allanglen/c172-flight-sim-panel/docs/assets/images/bendix-king-kt76c/bendix_king_kt76c_faceplate.jpg

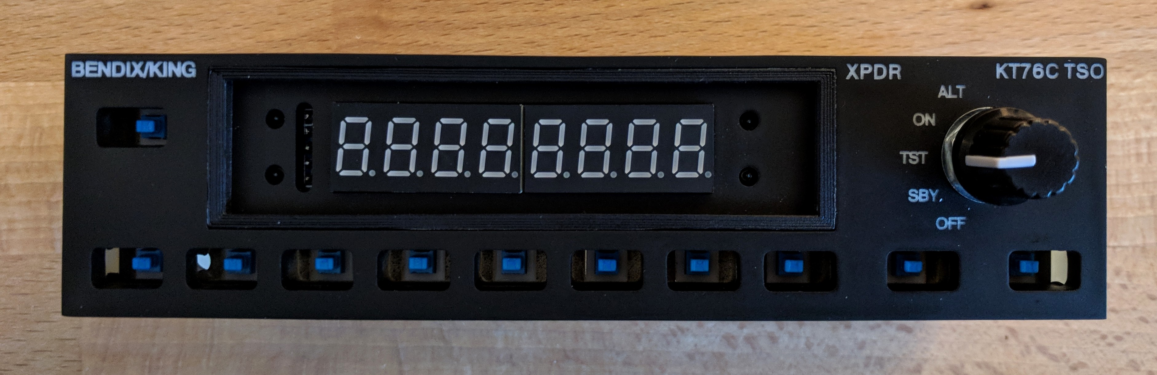
docs/assets/images/bendix-king-kt76c/bendix_king_kt76c_faceplate.jpg
