allanglen/c172-flight-sim-panel/docs/assets/images/docs/dusk.jpg

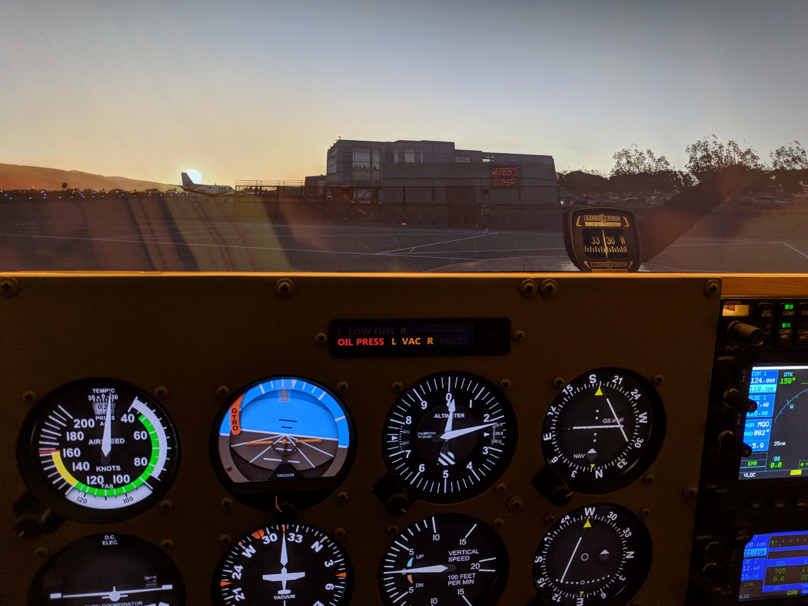
docs/assets/images/docs/dusk.jpg
