allanglen/c172-flight-sim-panel/docs/assets/images/docs/panel_close.jpg

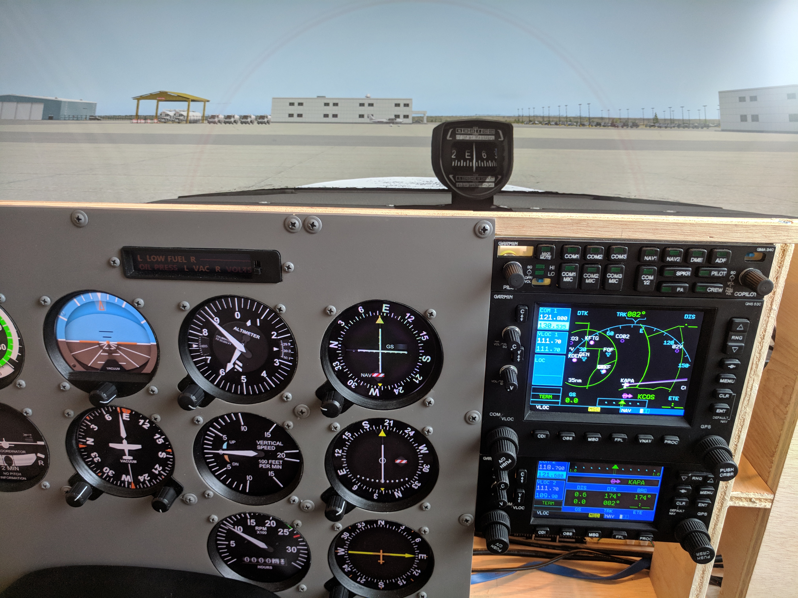
docs/assets/images/docs/panel_close.jpg
