allanglen/c172-flight-sim-panel/docs/assets/images/flap-control-panel/flap_faceplate.jpg

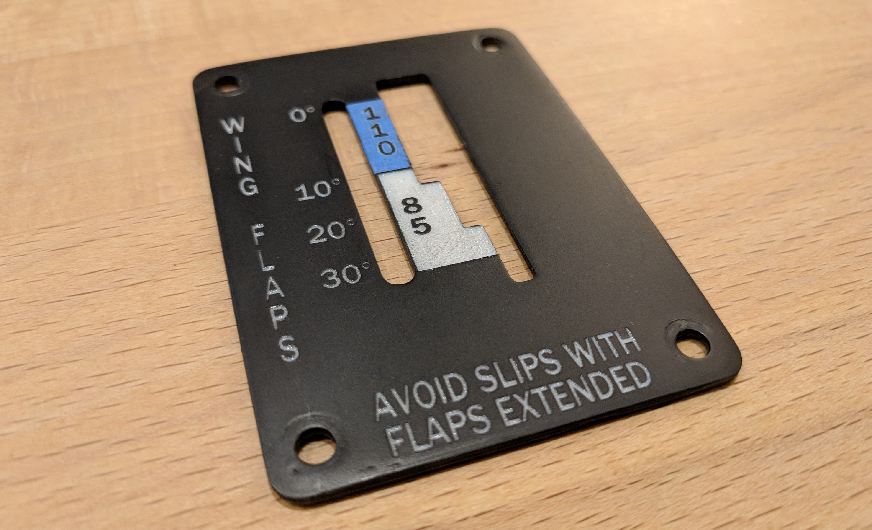
docs/assets/images/flap-control-panel/flap_faceplate.jpg
