allanglen/c172-flight-sim-panel/docs/assets/images/flap-control-panel/flap_lever_mount_rear.jpg

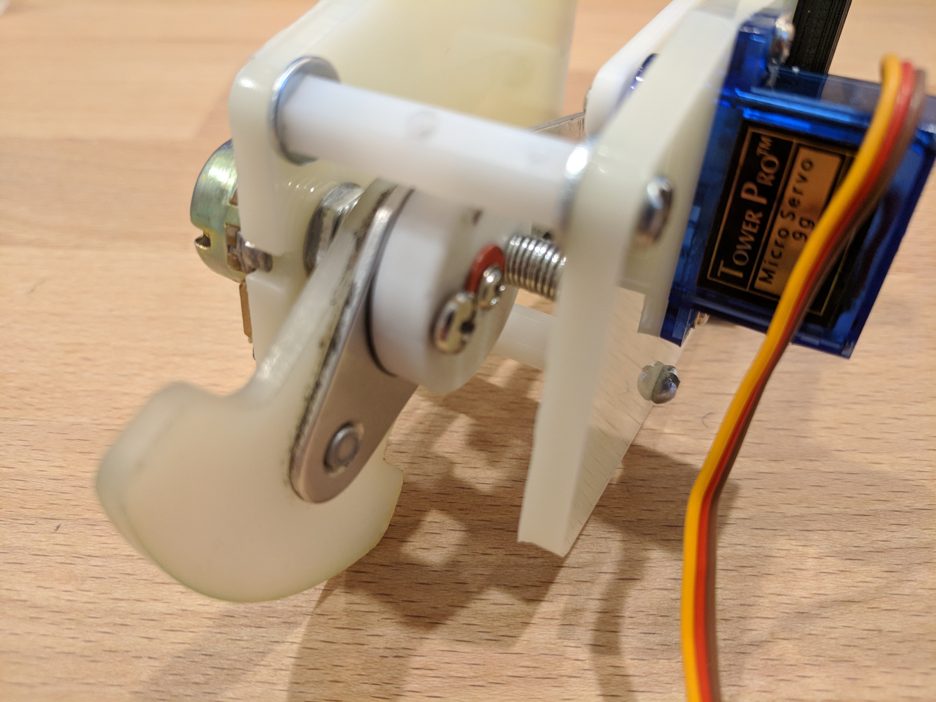
docs/assets/images/flap-control-panel/flap_lever_mount_rear.jpg
