allanglen/c172-flight-sim-panel/docs/assets/images/flap-control-panel/flaps_frame.jpg

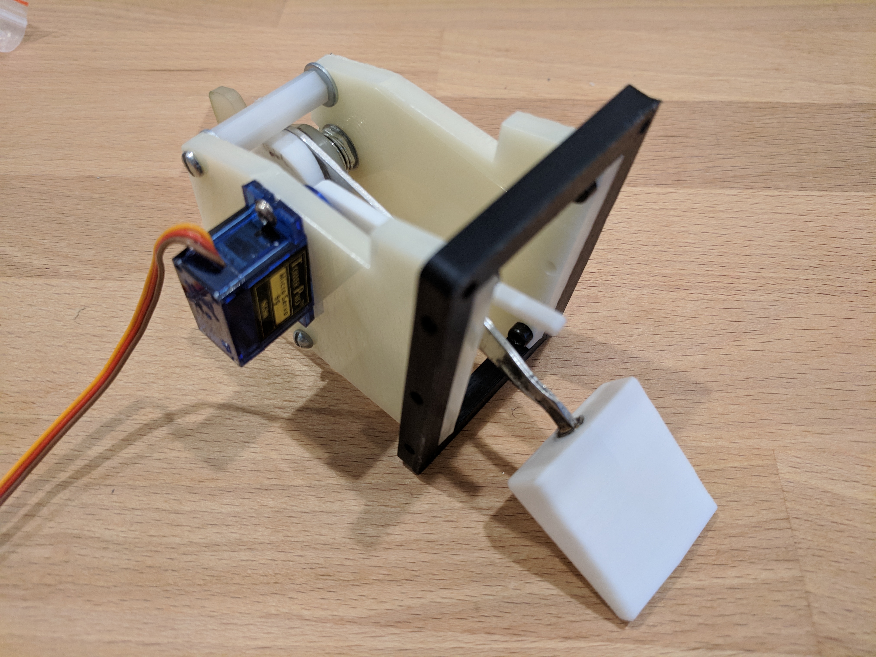
docs/assets/images/flap-control-panel/flaps_frame.jpg
