allanglen/c172-flight-sim-panel/docs/assets/images/flap-control-panel/flaps_panel.jpg

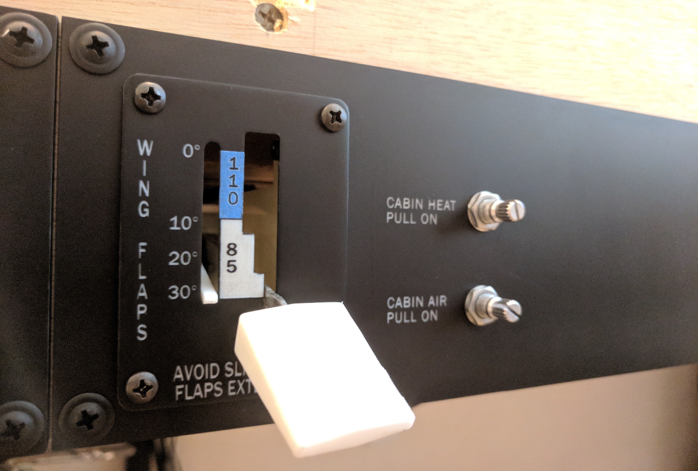
docs/assets/images/flap-control-panel/flaps_panel.jpg
