allanglen/c172-flight-sim-panel/docs/assets/images/flap-control-panel/frame_mounting_bracket.jpg

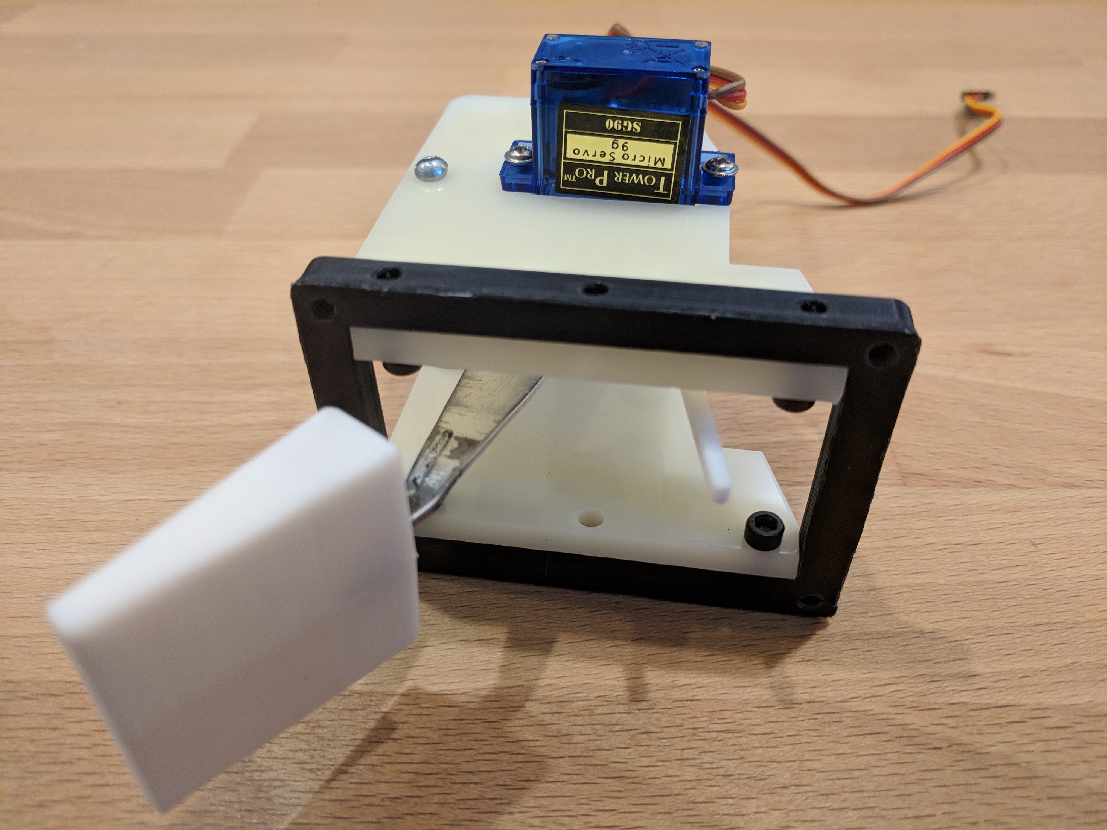
docs/assets/images/flap-control-panel/frame_mounting_bracket.jpg
