allanglen/c172-flight-sim-panel/docs/assets/images/frame/frame.jpg

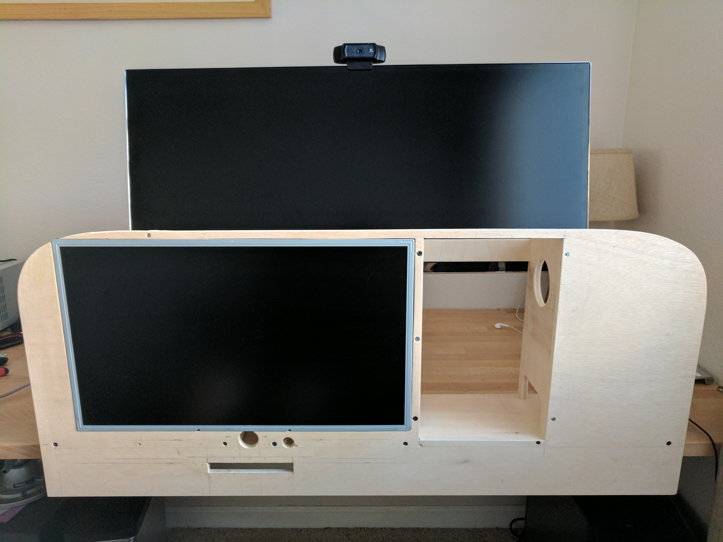
docs/assets/images/frame/frame.jpg
