allanglen/c172-flight-sim-panel/docs/assets/images/garmin-gns-430/display_rear.jpg

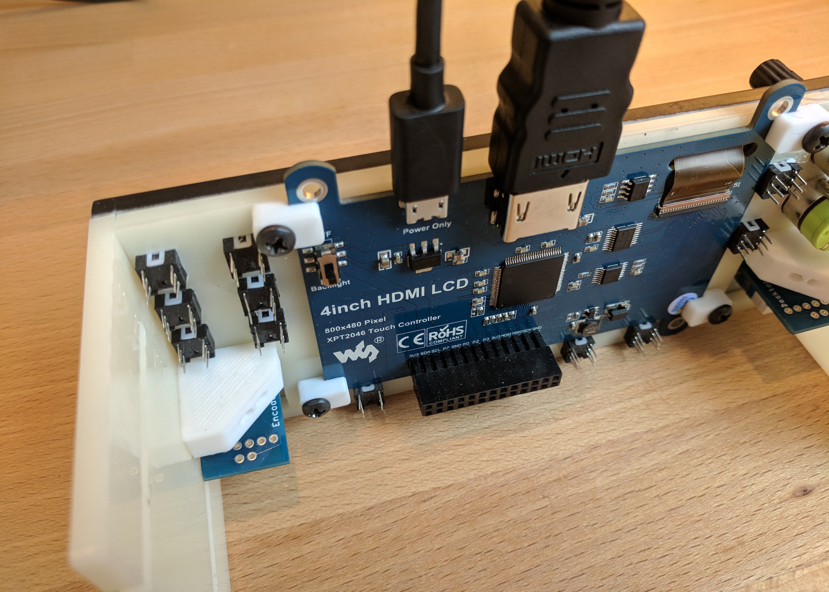
docs/assets/images/garmin-gns-430/display_rear.jpg
