allanglen/c172-flight-sim-panel/docs/assets/images/garmin-gns-430/frame_mount.jpg

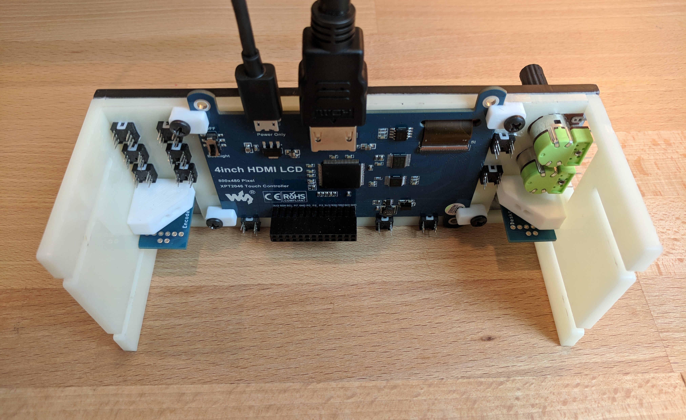
docs/assets/images/garmin-gns-430/frame_mount.jpg
