allanglen/c172-flight-sim-panel/docs/assets/images/garmin-gns-430/garmin_gns_430_map.jpg

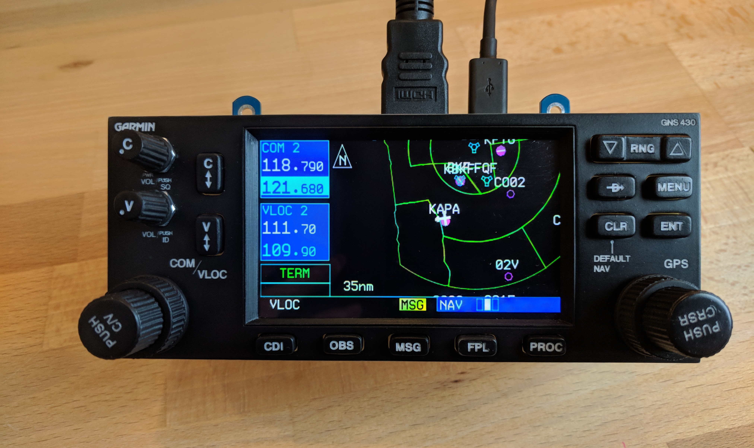
docs/assets/images/garmin-gns-430/garmin_gns_430_map.jpg
