allanglen/c172-flight-sim-panel/docs/assets/images/garmin-gns-430/garmin_gns_430_mounted_stack.jpg

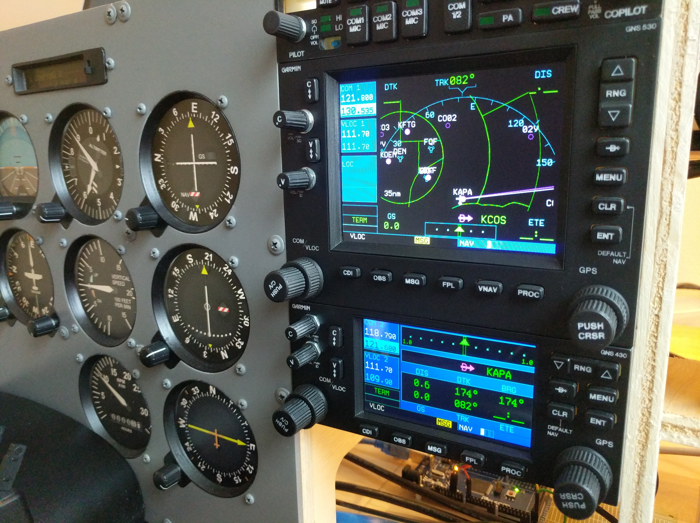
docs/assets/images/garmin-gns-430/garmin_gns_430_mounted_stack.jpg
