allanglen/c172-flight-sim-panel/docs/assets/images/garmin-gns-430/knob.jpg

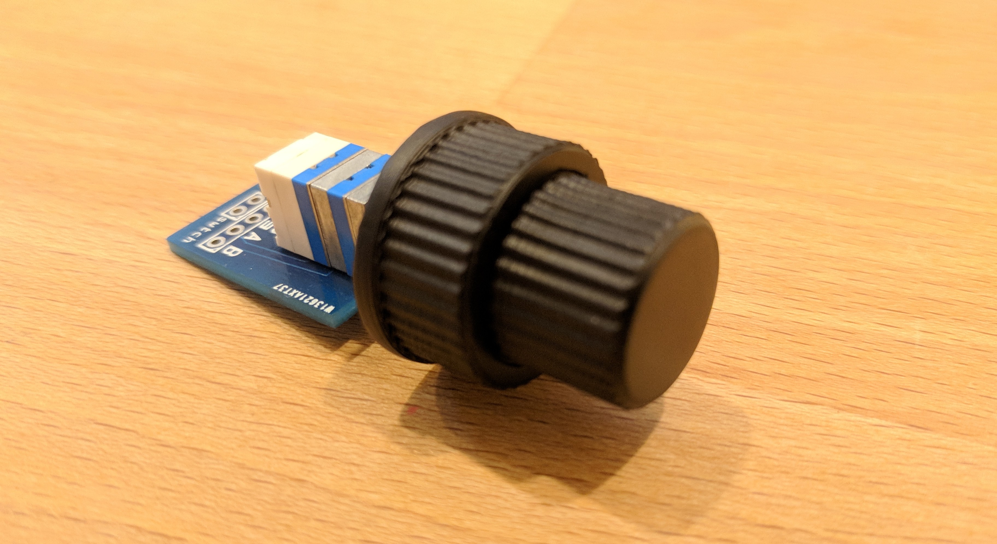
docs/assets/images/garmin-gns-430/knob.jpg
