allanglen/c172-flight-sim-panel/docs/assets/images/garmin-gns-530/frame_mount_left.jpg

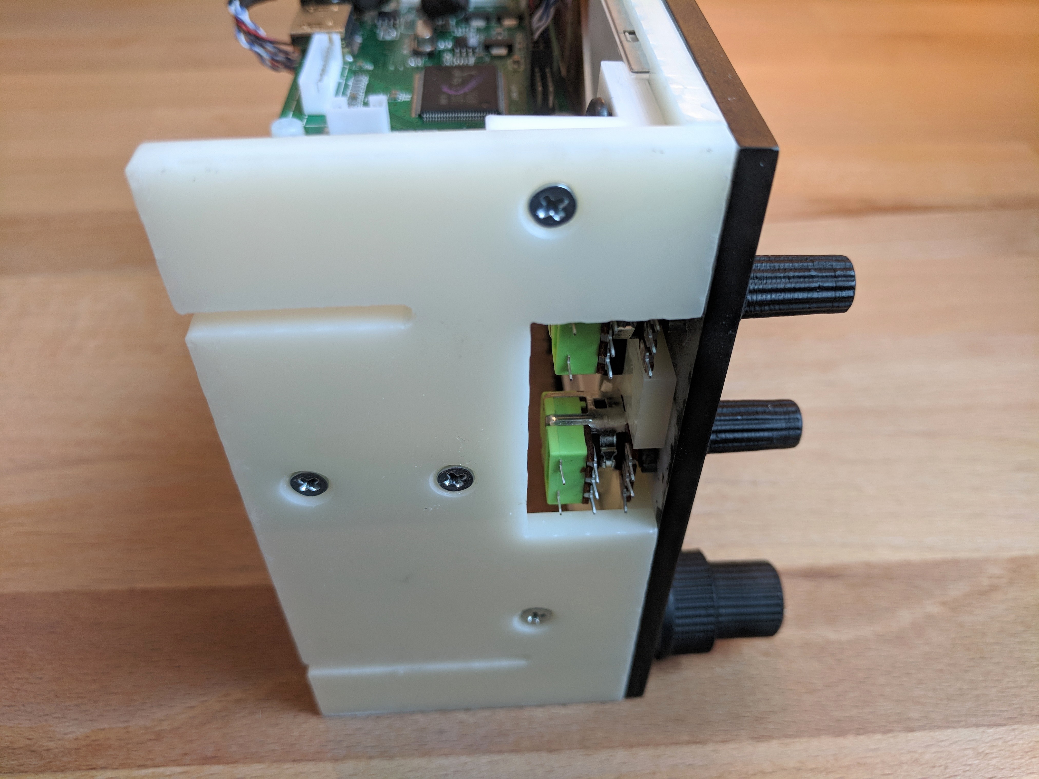
docs/assets/images/garmin-gns-530/frame_mount_left.jpg
