allanglen/c172-flight-sim-panel/docs/assets/images/garmin-gns-530/garmin_gns_530_mounted.jpg

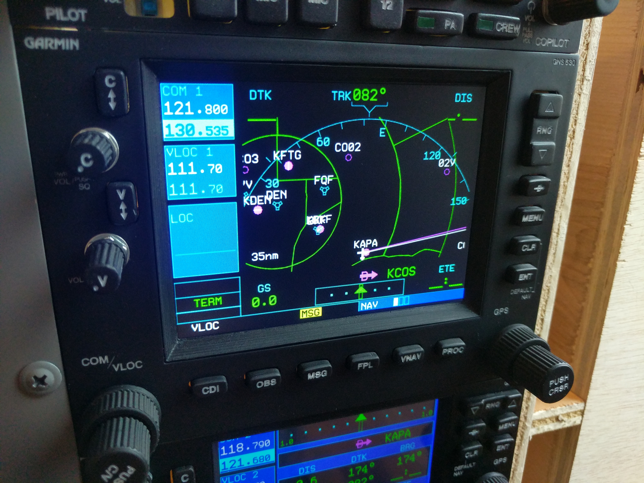
docs/assets/images/garmin-gns-530/garmin_gns_530_mounted.jpg
