allanglen/c172-flight-sim-panel/docs/assets/images/garmin-gns-530/garmin_gns_530_multiplexer.jpg

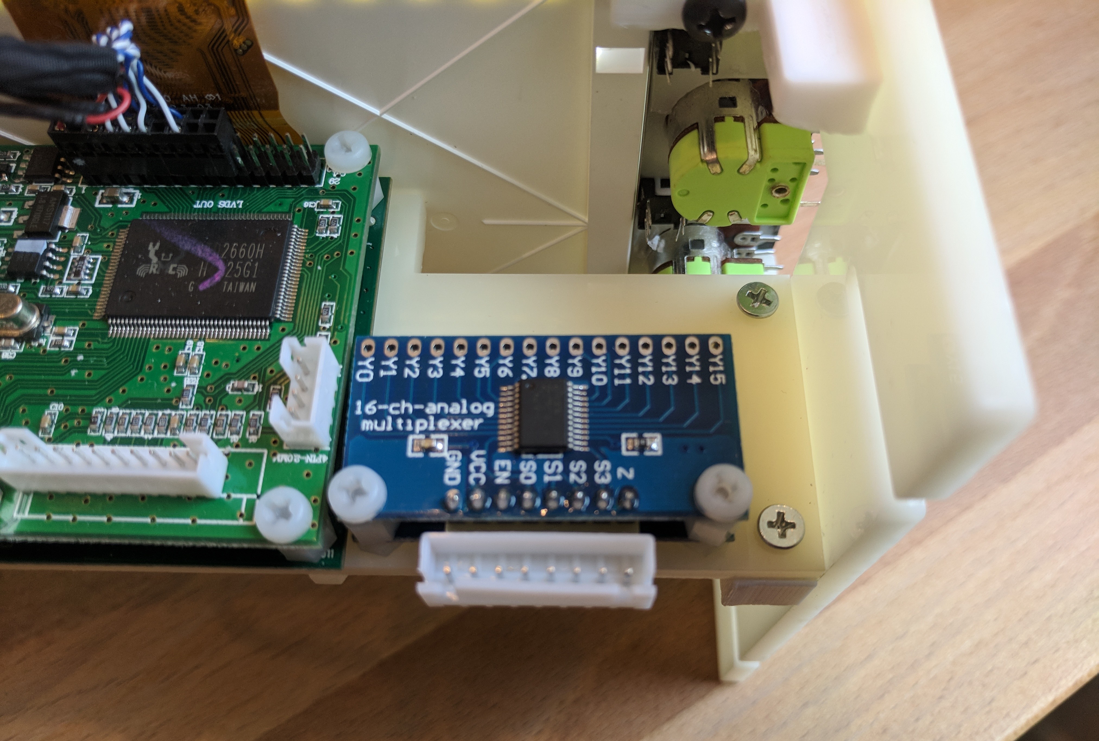
docs/assets/images/garmin-gns-530/garmin_gns_530_multiplexer.jpg
