allanglen/c172-flight-sim-panel/docs/assets/images/hero.jpg

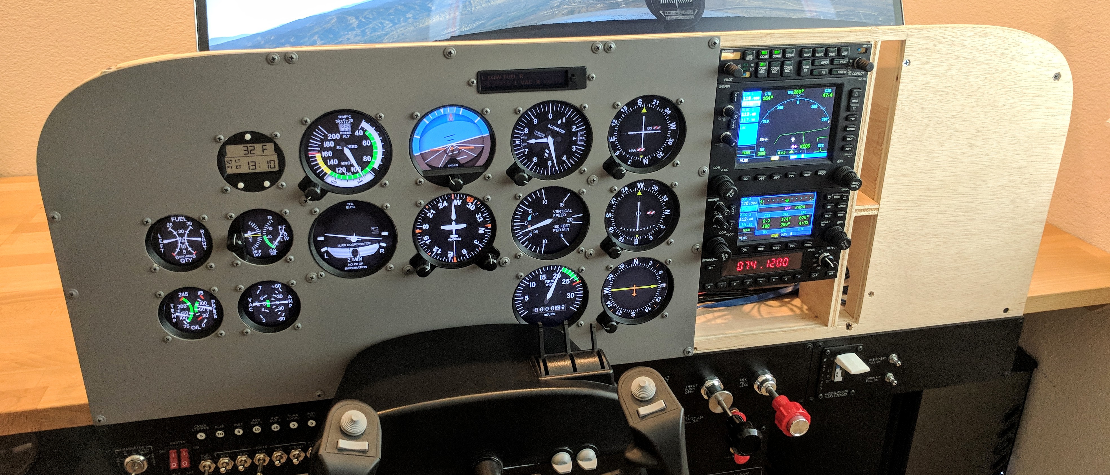
docs/assets/images/hero.jpg
