allanglen/c172-flight-sim-panel/docs/assets/images/highlight-avionics.jpg

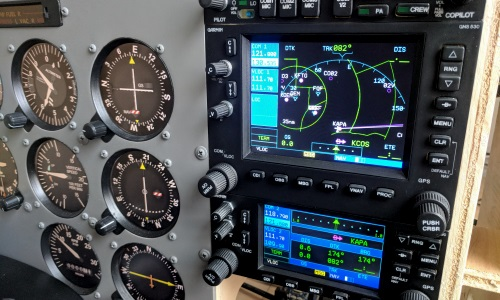
docs/assets/images/highlight-avionics.jpg
