allanglen/c172-flight-sim-panel/docs/assets/images/highlight-instrument-panel.jpg

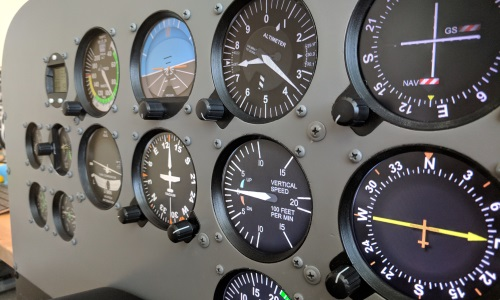
docs/assets/images/highlight-instrument-panel.jpg
