allanglen/c172-flight-sim-panel/docs/assets/images/highlight-switch-panel.jpg

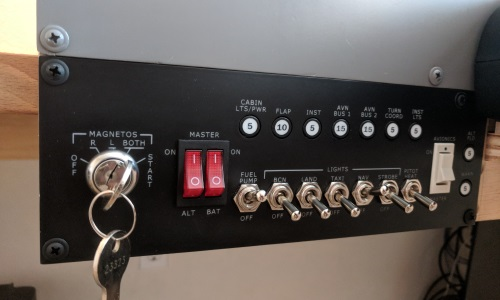
docs/assets/images/highlight-switch-panel.jpg
