allanglen/c172-flight-sim-panel/docs/assets/images/instrument-panel/air_manager.jpg

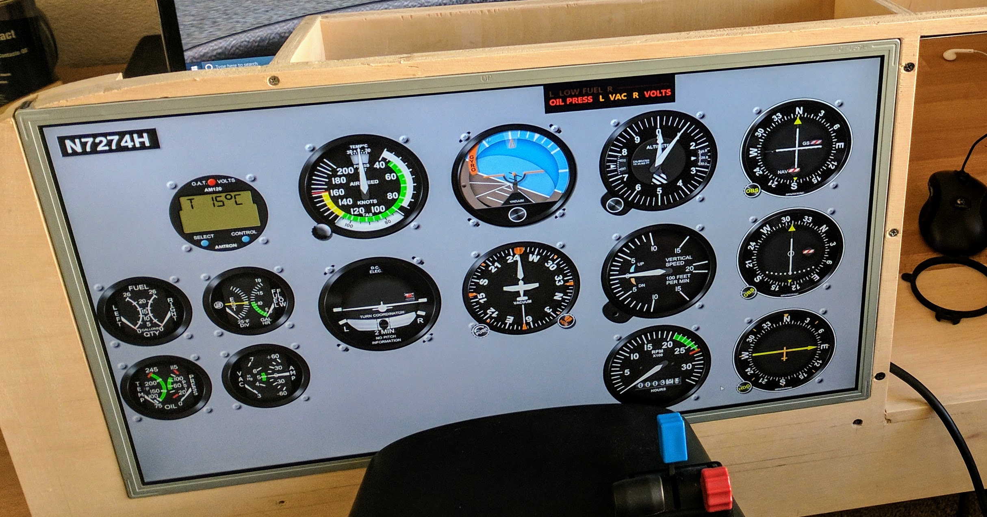
docs/assets/images/instrument-panel/air_manager.jpg
