allanglen/c172-flight-sim-panel/docs/assets/images/instrument-panel/bezel_encoder.jpg

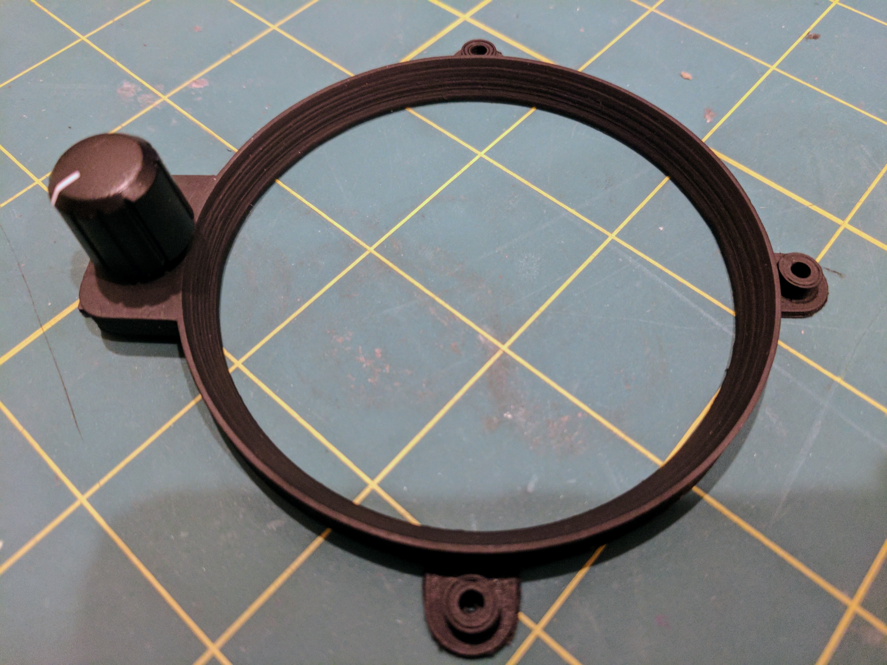
docs/assets/images/instrument-panel/bezel_encoder.jpg
