allanglen/c172-flight-sim-panel/docs/assets/images/instrument-panel/bezel_lcd.jpg

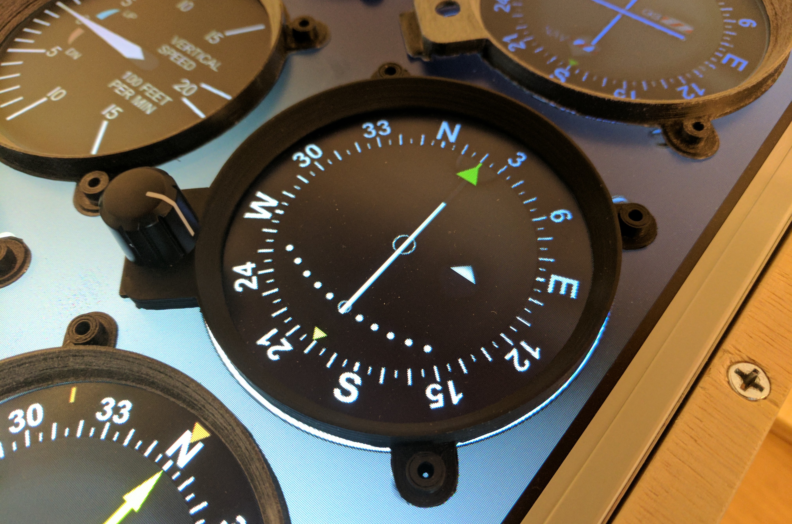
docs/assets/images/instrument-panel/bezel_lcd.jpg
