allanglen/c172-flight-sim-panel/docs/assets/images/instrument-panel/display_03.jpg

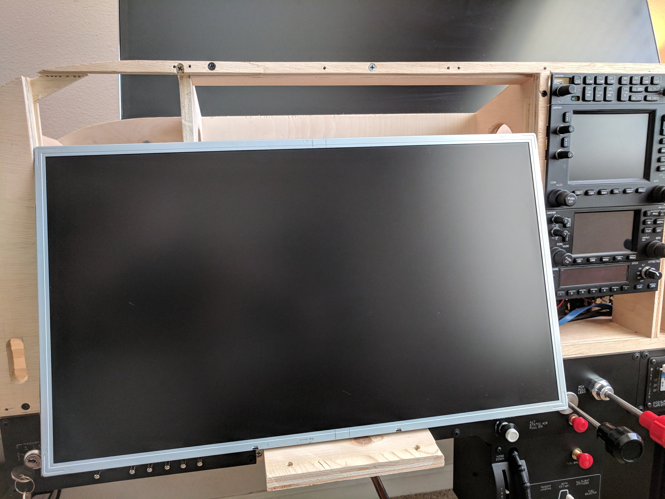
docs/assets/images/instrument-panel/display_03.jpg
