allanglen/c172-flight-sim-panel/docs/assets/images/instrument-panel/display_04.jpg

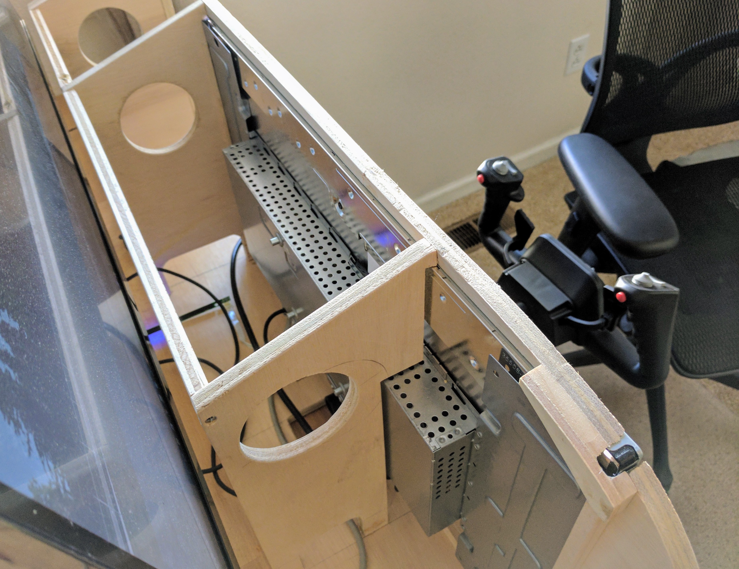
docs/assets/images/instrument-panel/display_04.jpg
