allanglen/c172-flight-sim-panel/docs/assets/images/instrument-panel/instrument_display.jpg

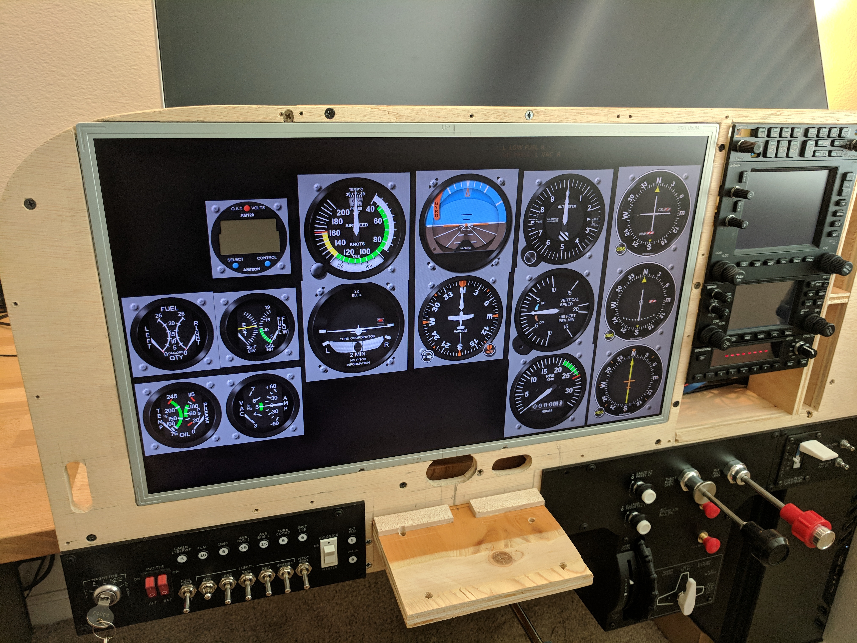
docs/assets/images/instrument-panel/instrument_display.jpg
