allanglen/c172-flight-sim-panel/docs/assets/images/instrument-panel/instrument_panel.jpg

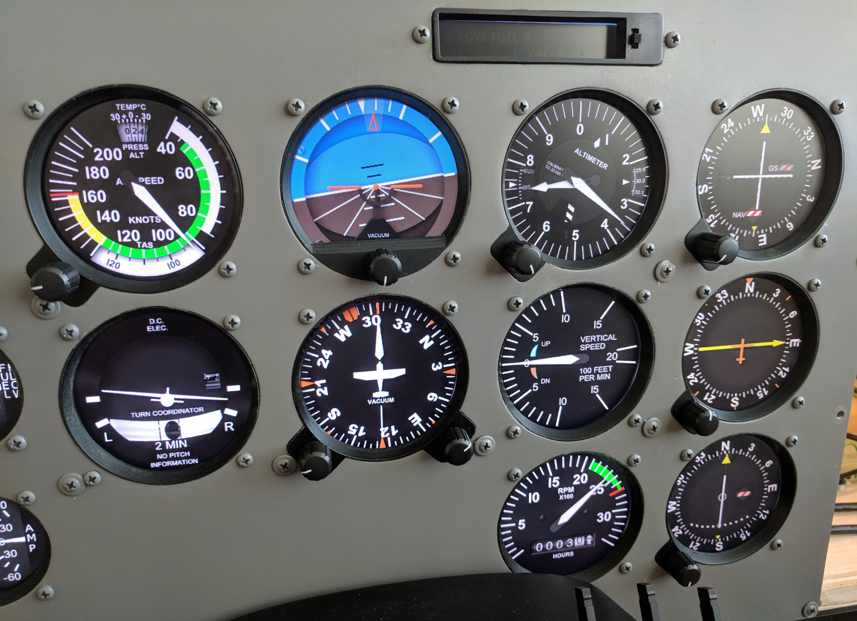
docs/assets/images/instrument-panel/instrument_panel.jpg
