allanglen/c172-flight-sim-panel/docs/assets/images/instrument-panel/instrument_panel_03.jpg

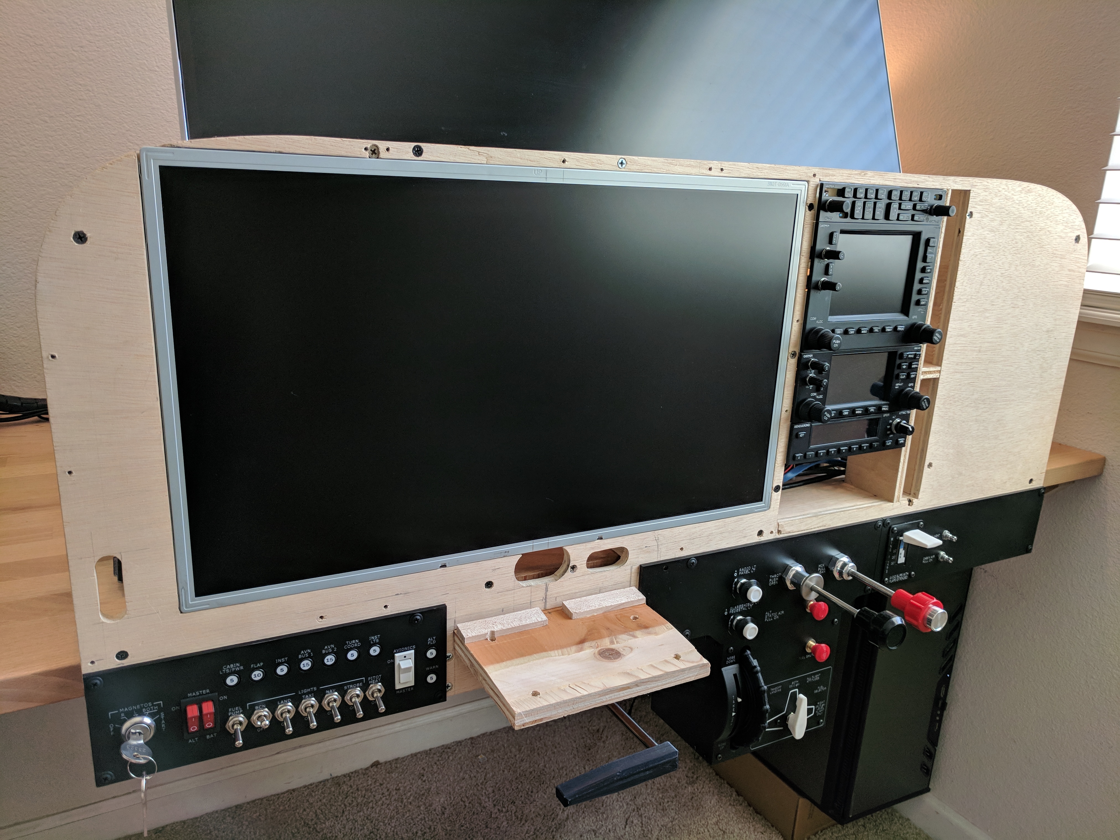
docs/assets/images/instrument-panel/instrument_panel_03.jpg
