allanglen/c172-flight-sim-panel/docs/assets/images/instrument-panel/panel_02.jpg

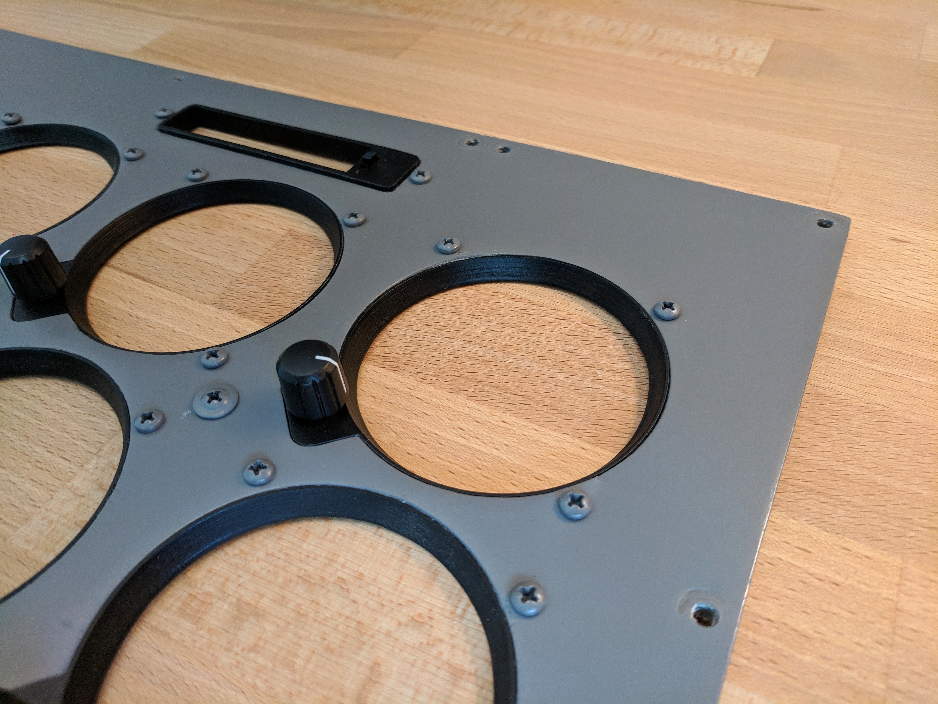
docs/assets/images/instrument-panel/panel_02.jpg
