allanglen/c172-flight-sim-panel/docs/assets/images/instrument-panel/panel_attached_02.jpg

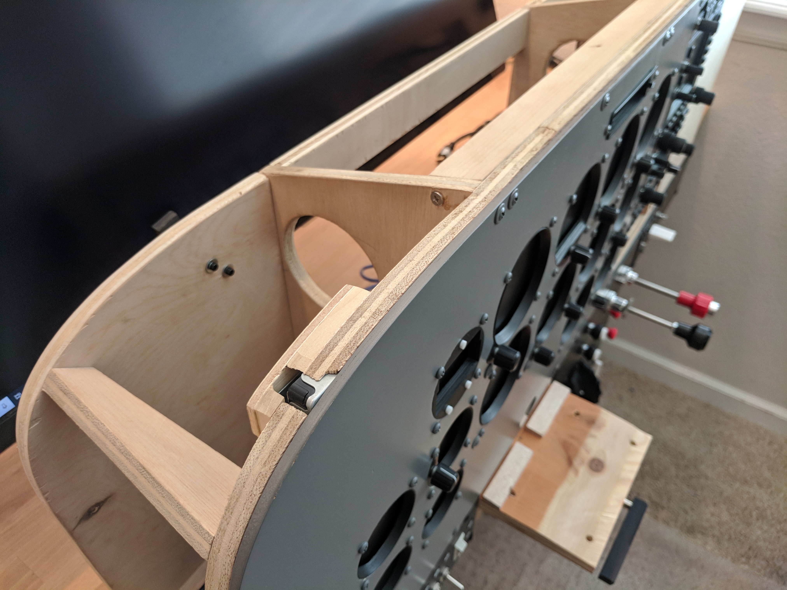
docs/assets/images/instrument-panel/panel_attached_02.jpg
