allanglen/c172-flight-sim-panel/docs/assets/images/instrument-panel/panel_rear_04.jpg

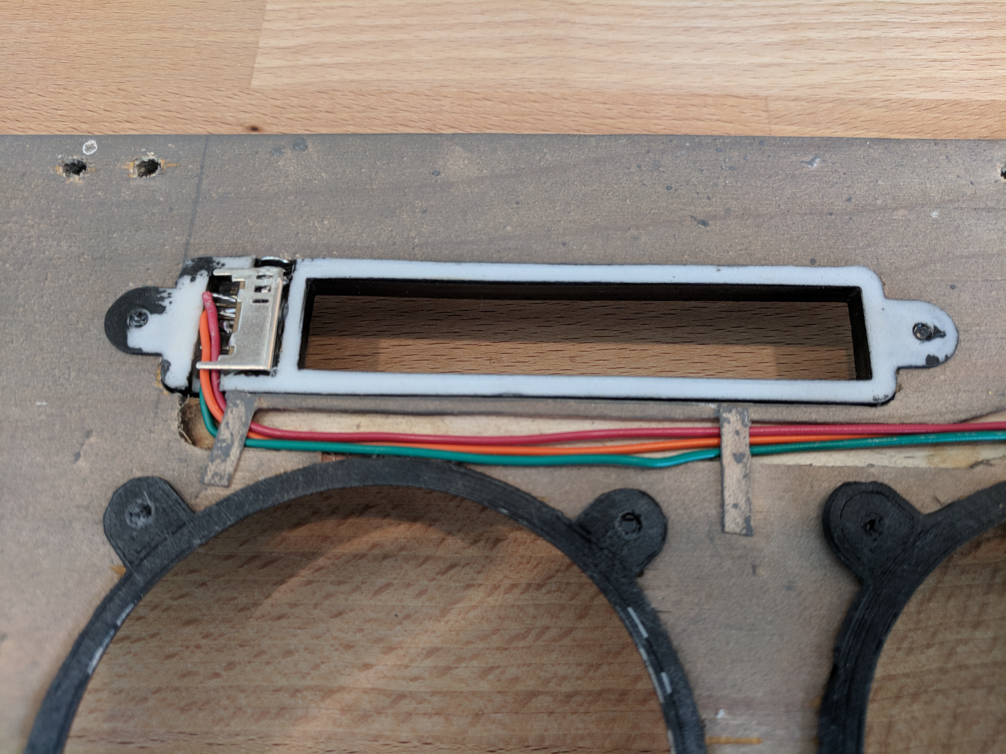
docs/assets/images/instrument-panel/panel_rear_04.jpg
