allanglen/c172-flight-sim-panel/docs/assets/images/instrument-panel/panel_rear_05.jpg

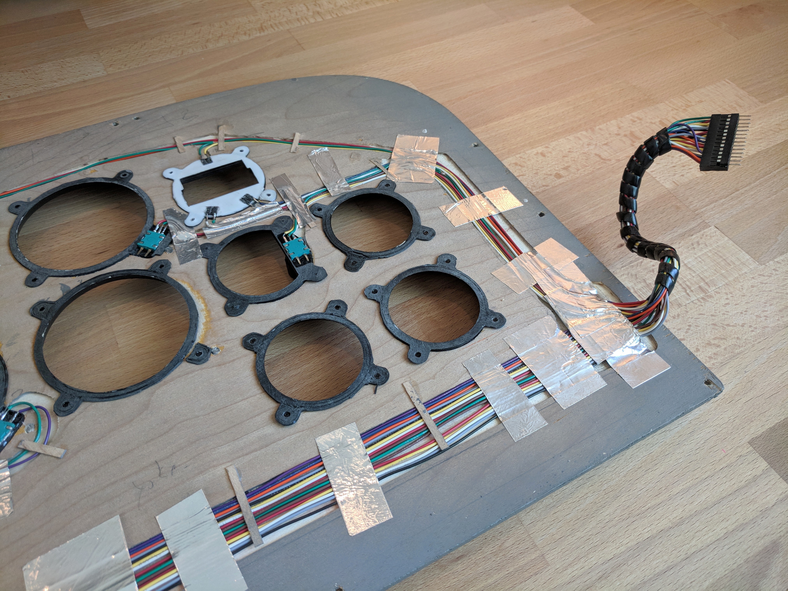
docs/assets/images/instrument-panel/panel_rear_05.jpg
