allanglen/c172-flight-sim-panel/docs/assets/images/key-switch/key_switch_animation.gif

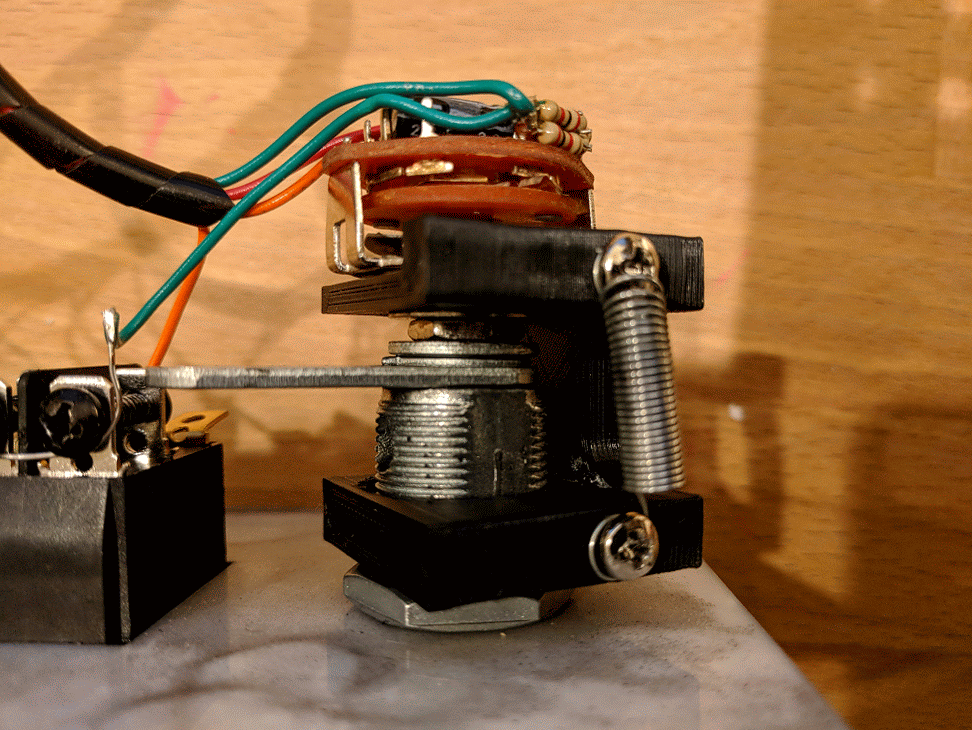
docs/assets/images/key-switch/key_switch_animation.gif
