allanglen/c172-flight-sim-panel/docs/assets/images/key-switch/key_switch_mounted.jpg

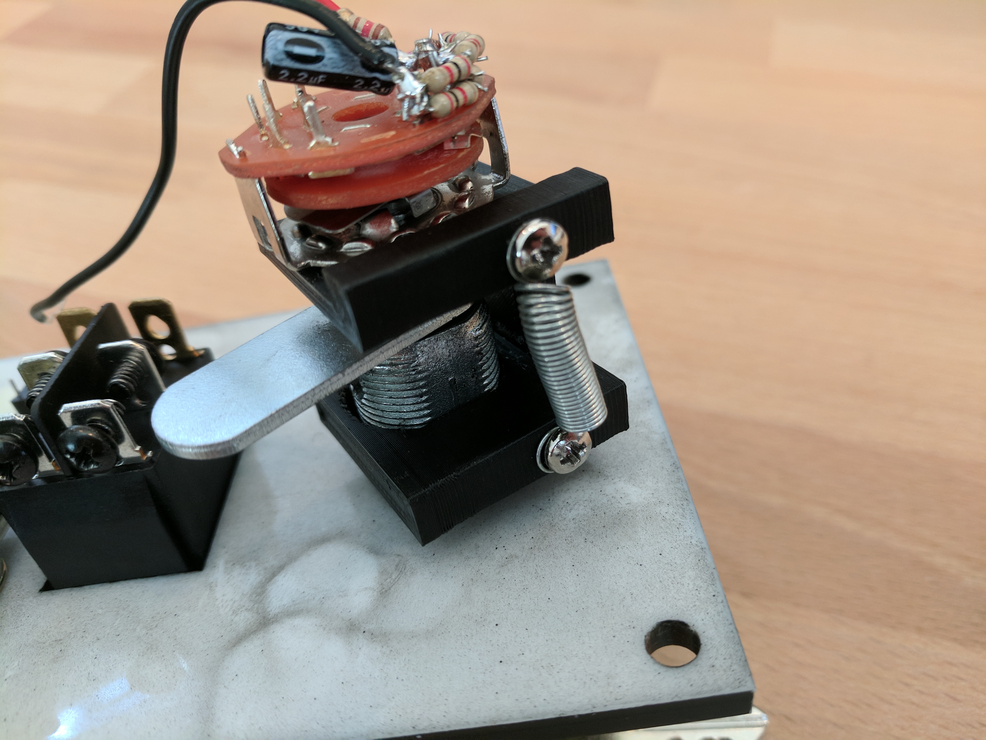
docs/assets/images/key-switch/key_switch_mounted.jpg
