allanglen/c172-flight-sim-panel/docs/assets/images/rudder-pedals/rudder_pedal_left.jpg

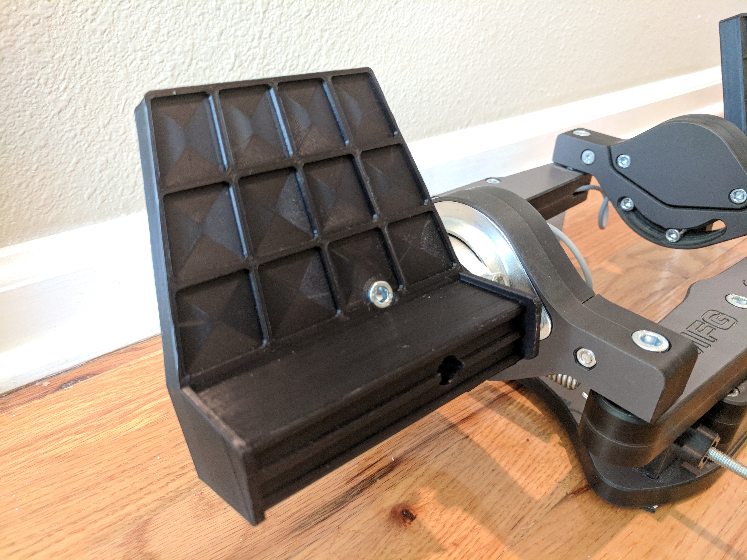
docs/assets/images/rudder-pedals/rudder_pedal_left.jpg
