allanglen/c172-flight-sim-panel/docs/assets/images/rudder-pedals/rudder_pedal_rear.jpg

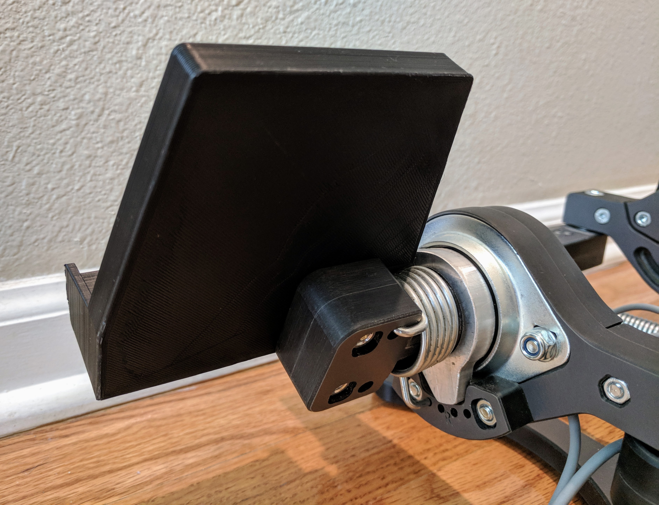
docs/assets/images/rudder-pedals/rudder_pedal_rear.jpg
