allanglen/c172-flight-sim-panel/docs/assets/images/rudder-pedals/rudder_pedal_right.jpg

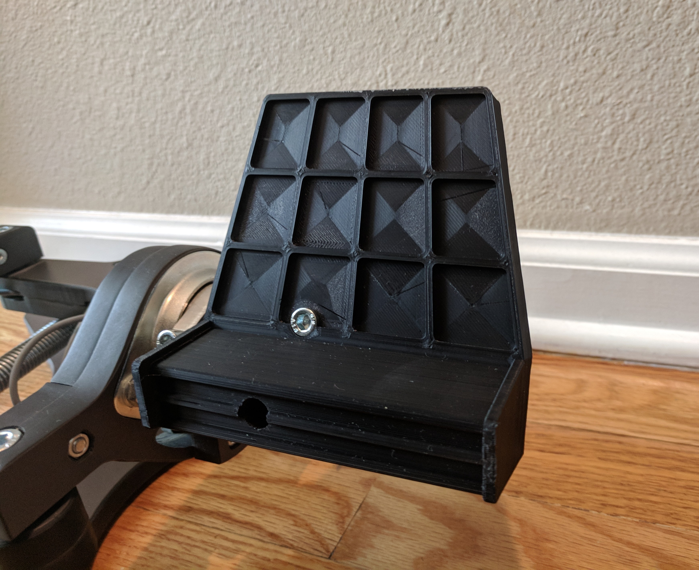
docs/assets/images/rudder-pedals/rudder_pedal_right.jpg
