allanglen/c172-flight-sim-panel/docs/assets/images/rudder-pedals/rudder_pedals.jpg

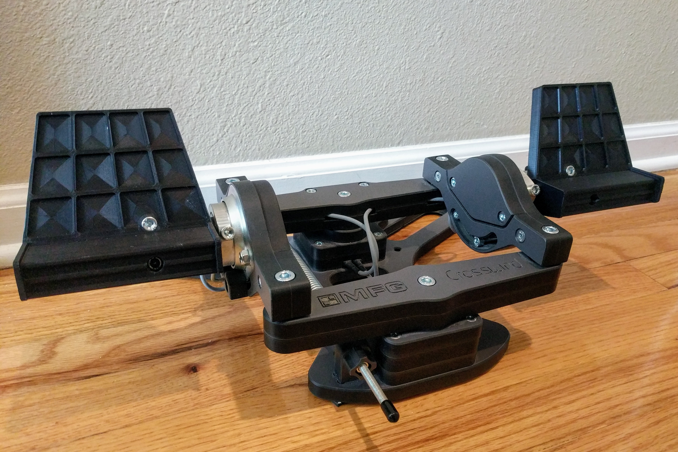
docs/assets/images/rudder-pedals/rudder_pedals.jpg
