allanglen/c172-flight-sim-panel/docs/assets/images/switch-panel/fuse_mount.jpg

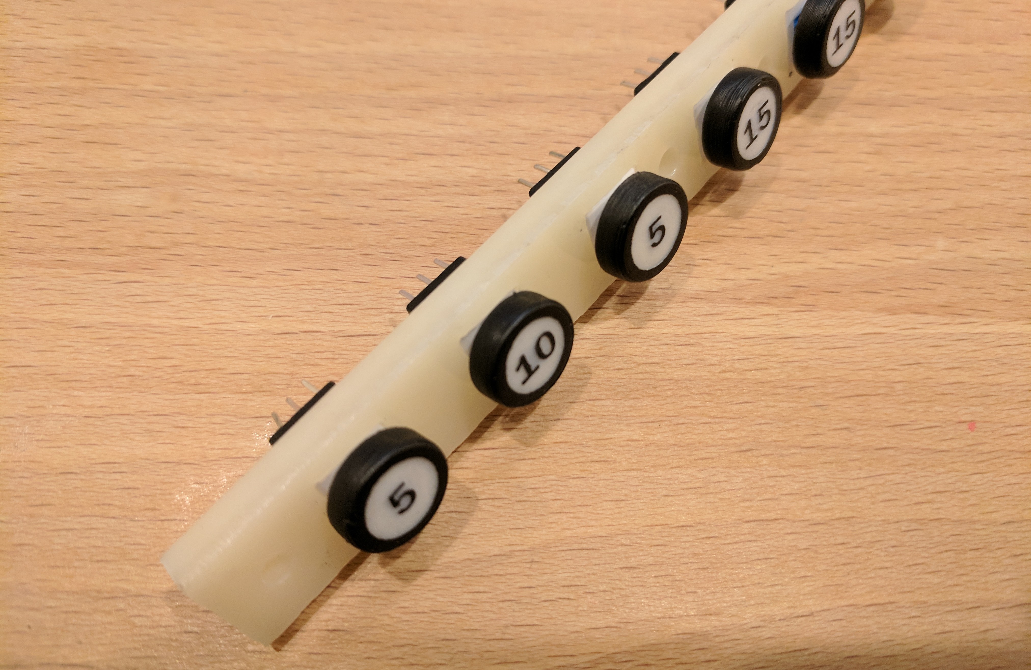
docs/assets/images/switch-panel/fuse_mount.jpg
