allanglen/c172-flight-sim-panel/docs/assets/images/switch-panel/fuses.jpg

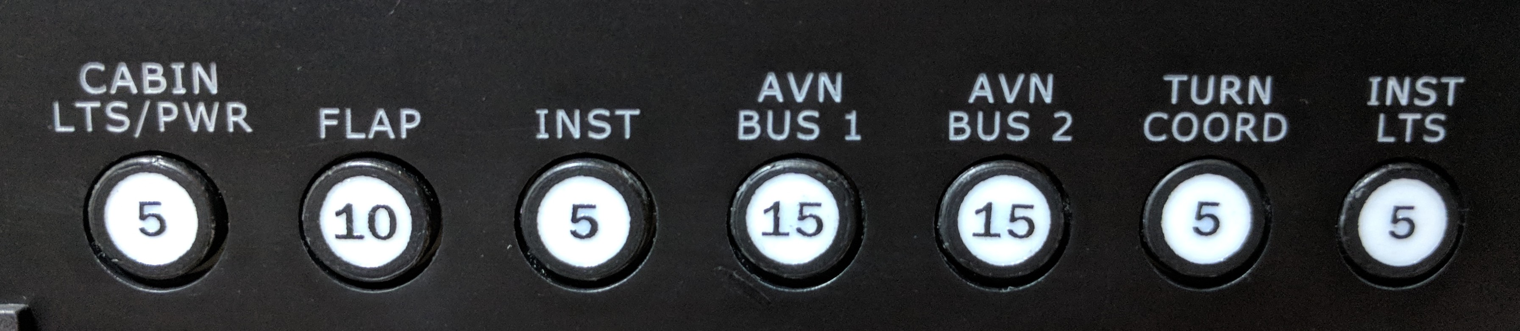
docs/assets/images/switch-panel/fuses.jpg
