allanglen/c172-flight-sim-panel/docs/assets/images/throttle-mixture-panel/rheostat_knobs.jpg

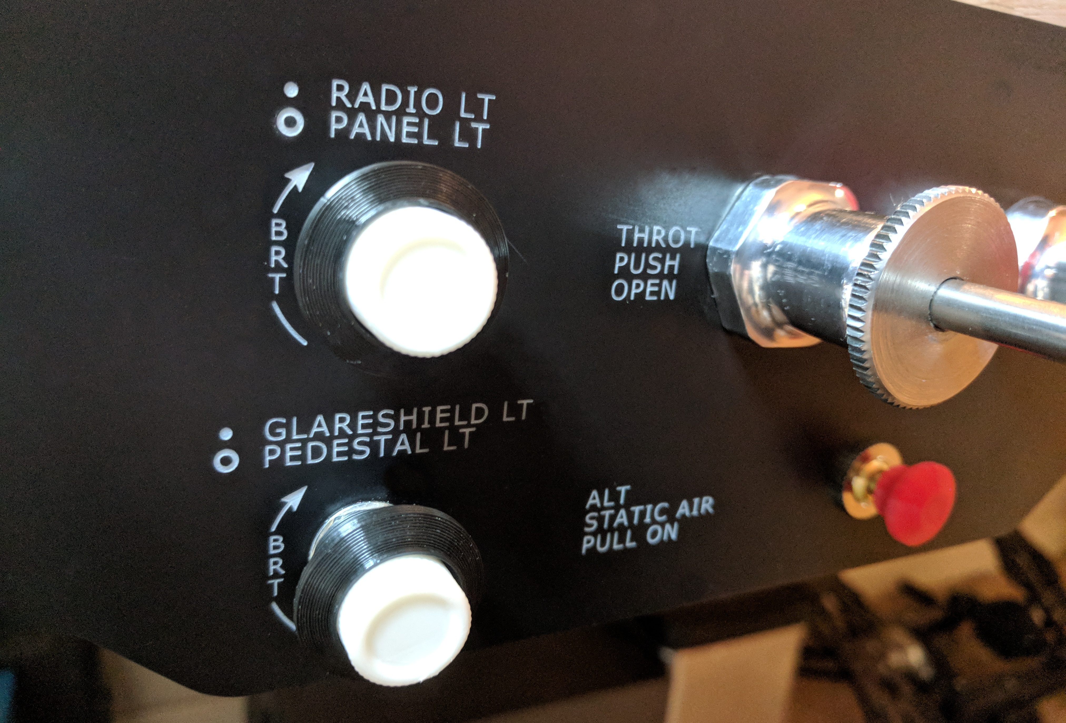
docs/assets/images/throttle-mixture-panel/rheostat_knobs.jpg
