allanglen/c172-flight-sim-panel/docs/assets/images/throttle-mixture-panel/throttle_mixture_panel.jpg

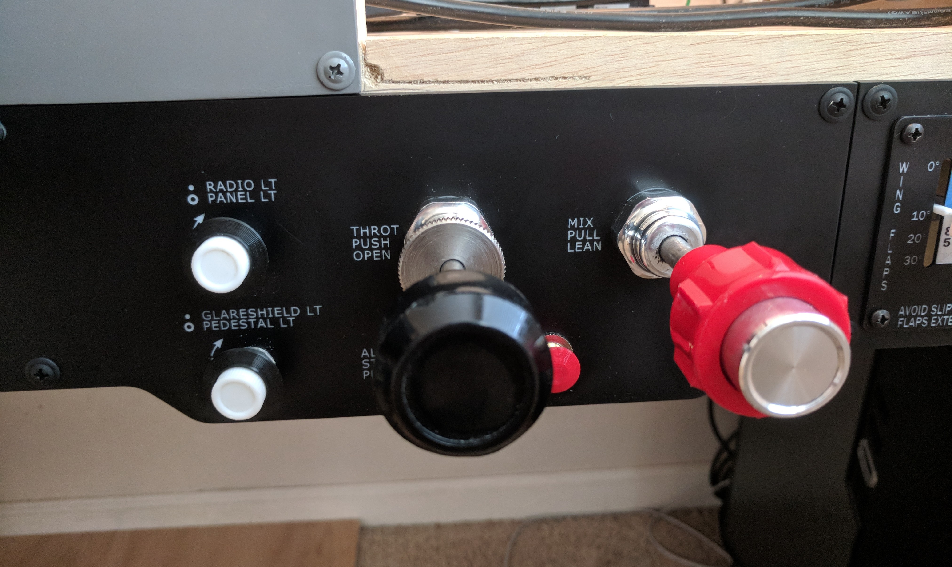
docs/assets/images/throttle-mixture-panel/throttle_mixture_panel.jpg
