allanglen/c172-flight-sim-panel/docs/assets/images/trim-wheel/fuel_selector.jpg

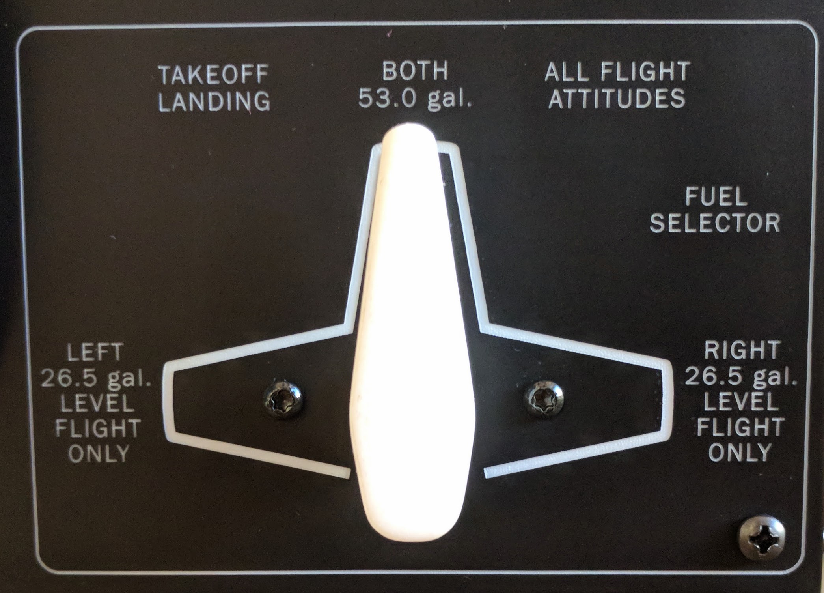
docs/assets/images/trim-wheel/fuel_selector.jpg
