allanglen/c172-flight-sim-panel/docs/assets/images/trim-wheel/trim_wheel_close.jpg

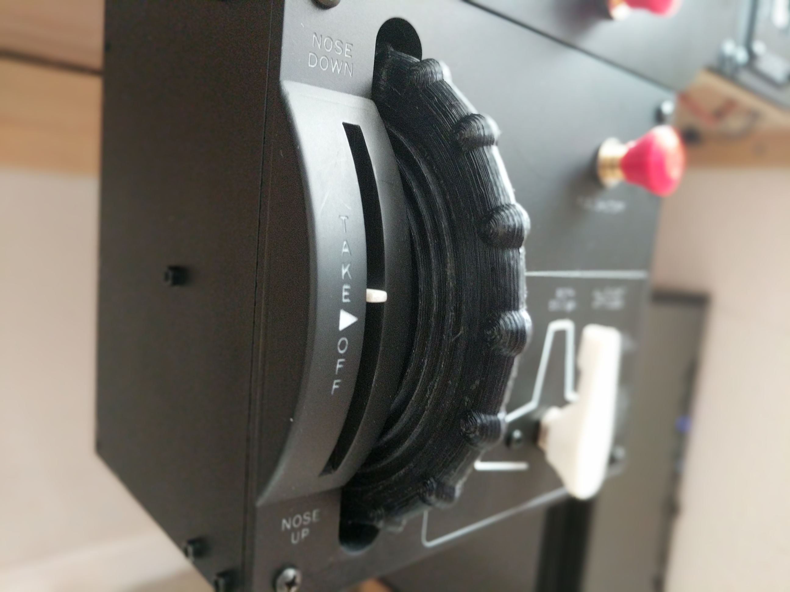
docs/assets/images/trim-wheel/trim_wheel_close.jpg
