allanglen/c172-flight-sim-panel/docs/assets/images/trim-wheel/trim_wheel_faceplate.jpg

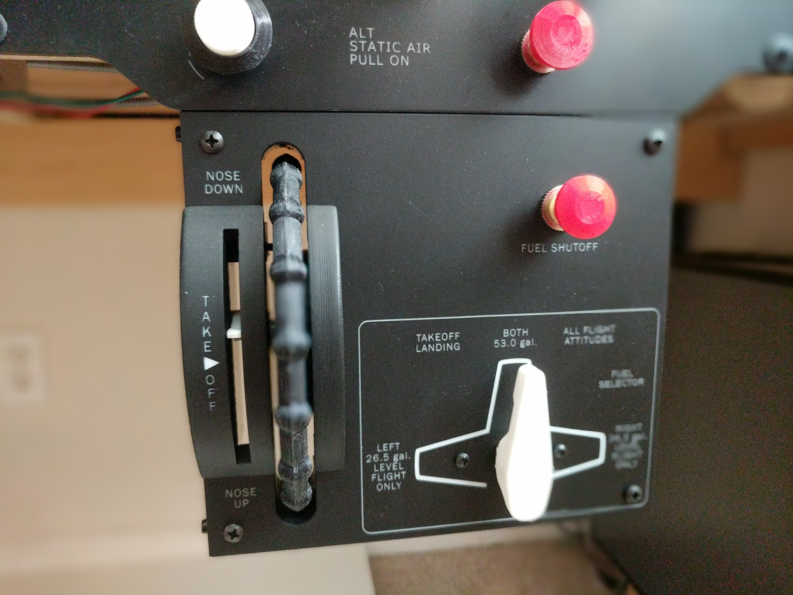
docs/assets/images/trim-wheel/trim_wheel_faceplate.jpg
