allanglen/c172-flight-sim-panel/docs/assets/images/yoke-mount/yoke_mount.jpg

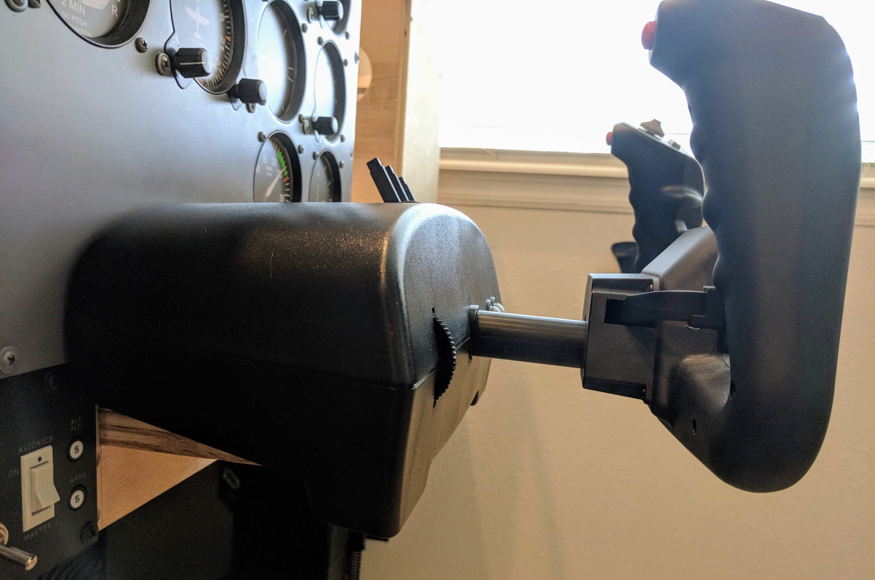
docs/assets/images/yoke-mount/yoke_mount.jpg
