allanglen/c172-flight-sim-panel/instrument_panel/images/instrument_panel_left_view.jpg

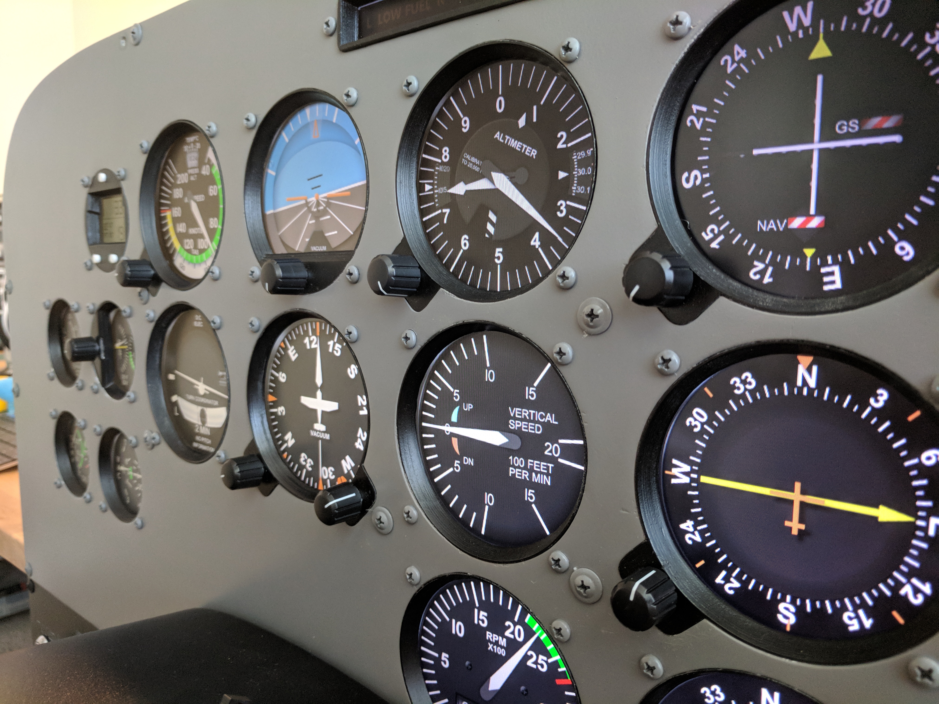
instrument_panel/images/instrument_panel_left_view.jpg
