allanglen/c172-flight-sim-panel/parts/avionics/garmin-gns-430/garmin_430_photo.png

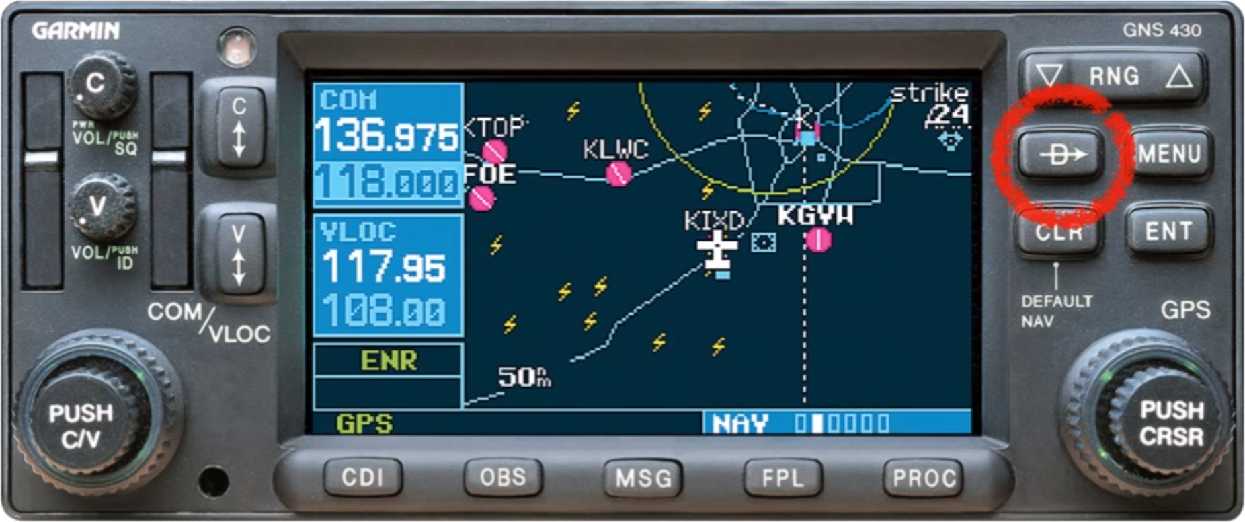
parts/avionics/garmin-gns-430/garmin_430_photo.png
