allanglen/c172-flight-sim-panel/parts/avionics/garmin-gns-530/garmin_gns_530.jpg

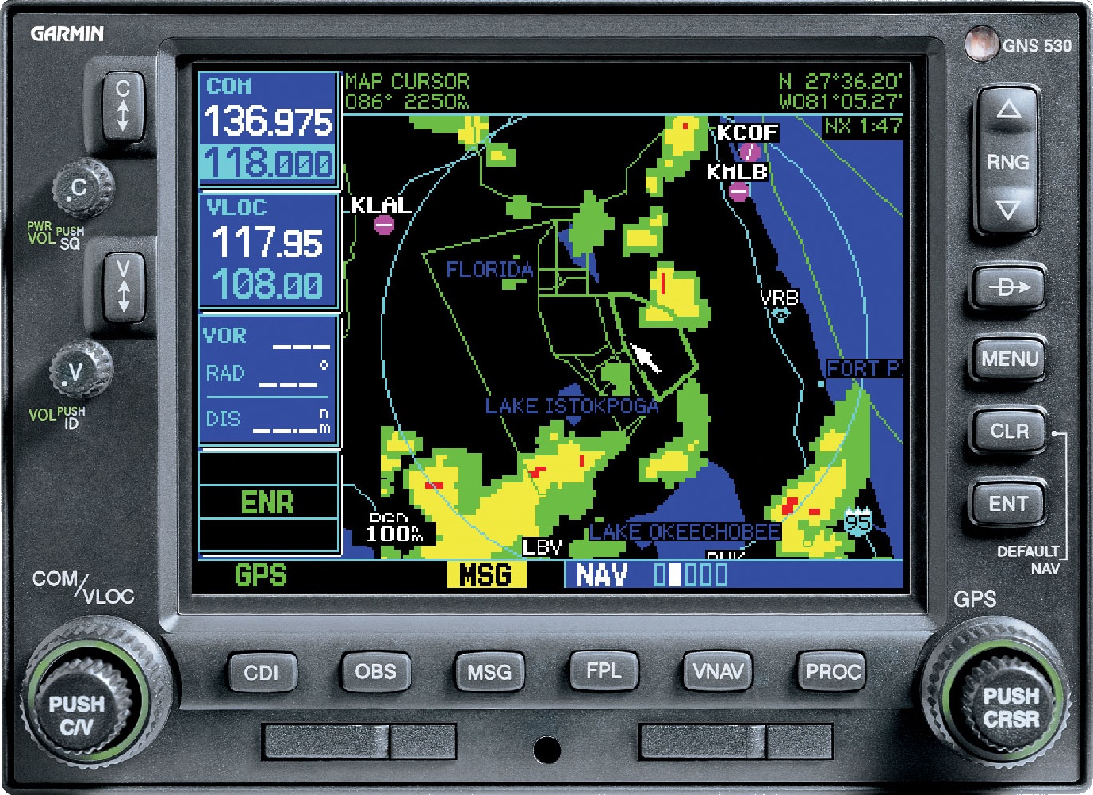
parts/avionics/garmin-gns-530/garmin_gns_530.jpg
