allanglen/c172-flight-sim-panel/parts/throttle-mixture-panel/statis_air_knob.FCStd

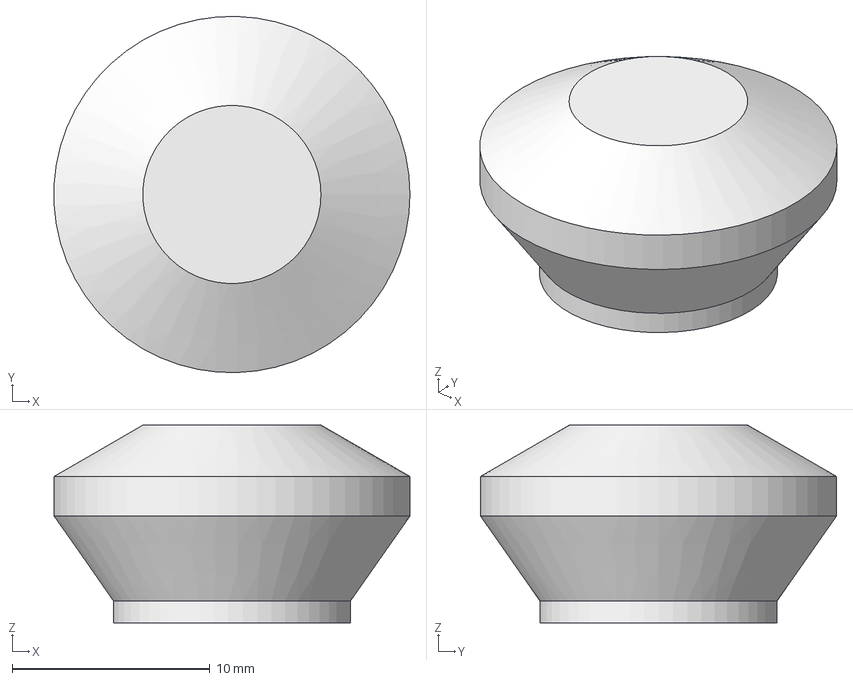
[picture p106: CAD file, 2018-01-21]
parts/throttle-mixture-panel/statis_air_knob.FCStd
18.0 x 18.0 x 10.0 mm
