allanglen/c172-flight-sim-panel/parts/avionics/bendix-king-kt-76c/bendix_king_kt_76c.FCStd

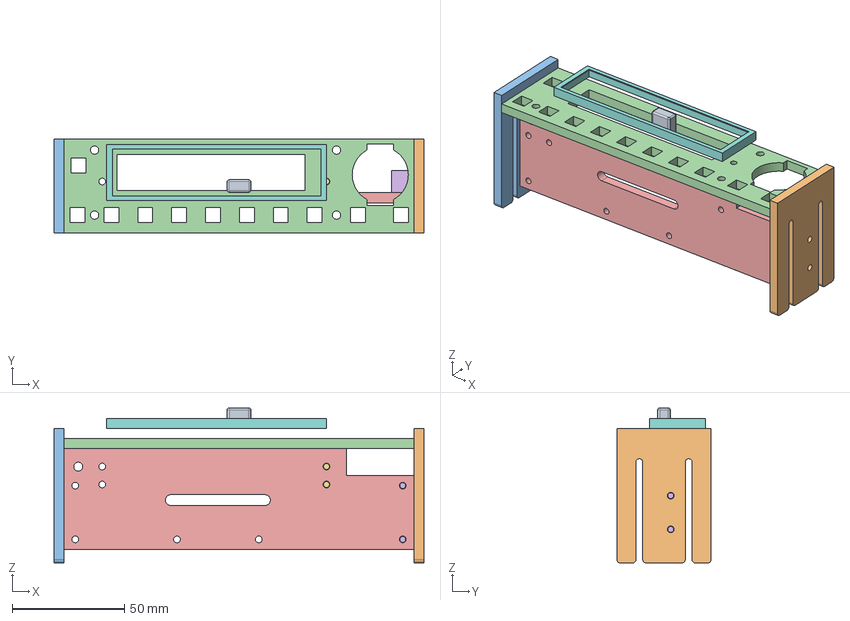
[picture p107: CAD file, 2018-05-28]
parts/avionics/bendix-king-kt-76c/bendix_king_kt_76c.FCStd
165.0 x 42.0 x 69.1 mm
Cut (button)
Pad (right side)
Pad (left side)
Pad (hardware mount)
Pad (electronics mount)
Pocket (side bracket side holes)
Pocket (front bracket front hole)
Cut (bezel)
