allanglen/c172-flight-sim-panel/parts/avionics/garmin-gns-430/preview.stl

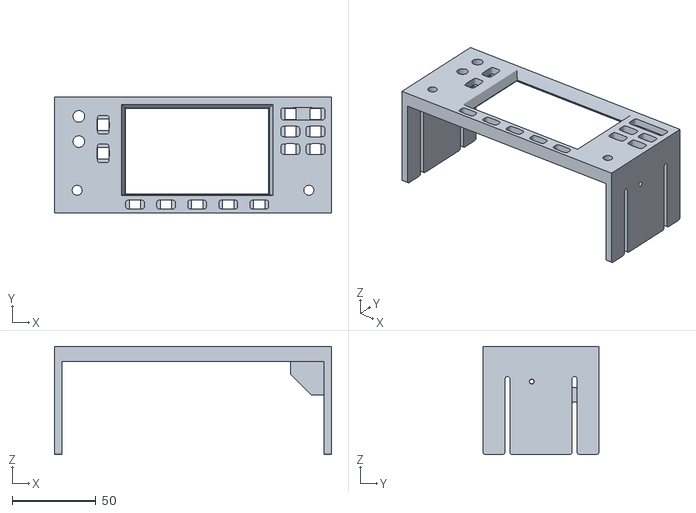
[picture p108: CAD file, 2018-01-07]
parts/avionics/garmin-gns-430/preview.stl
165.0 x 69.0 x 64.5
