allanglen/c172-flight-sim-panel/parts/avionics/garmin-gns-530/preview.stl

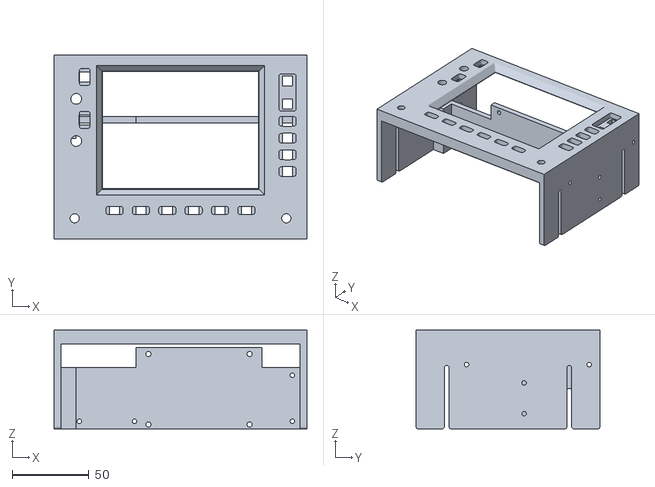
[picture p109: CAD file, 2018-01-21]
parts/avionics/garmin-gns-530/preview.stl
165.0 x 120.0 x 64.5
