allanglen/c172-flight-sim-panel/parts/instrument-panel/bezel_small.FCStd

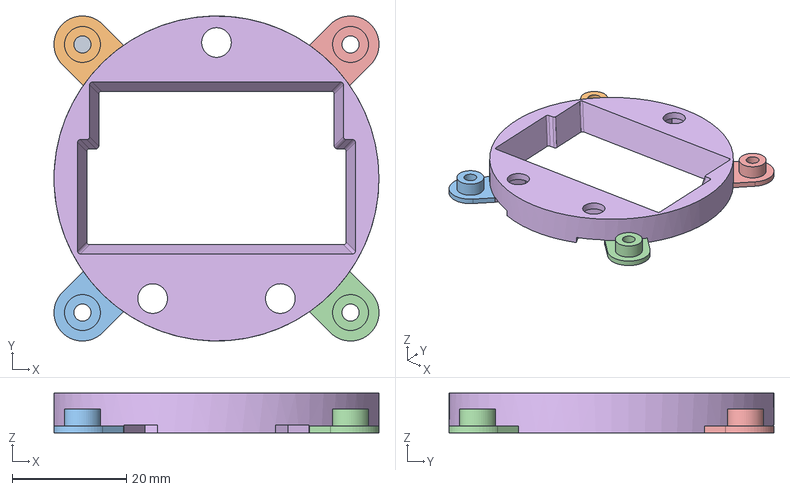
[picture p110: CAD file, 2017-12-05]
parts/instrument-panel/bezel_small.FCStd
57.0 x 57.0 x 7.00 mm
Pad (tab base)
Pocket (tab screw hole)
Tab (bottom left)
Tab (bottom right)
Tab (top right)
Cut (clock bezel)
