allanglen/c172-flight-sim-panel/parts/rudder-pedals/rudder_pedals.FCStd

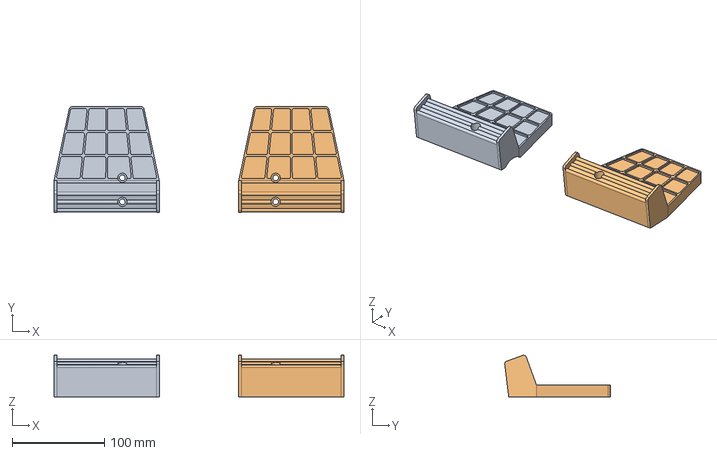
[picture p111: CAD file, 2018-03-21]
parts/rudder-pedals/rudder_pedals.FCStd
314.0 x 114.4 x 45.0 mm
Cut (pedal left)
Mirror (pedal right)
