allanglen/c172-flight-sim-panel/parts/avionics/bendix-king-kt-76c/side_bracket.stl

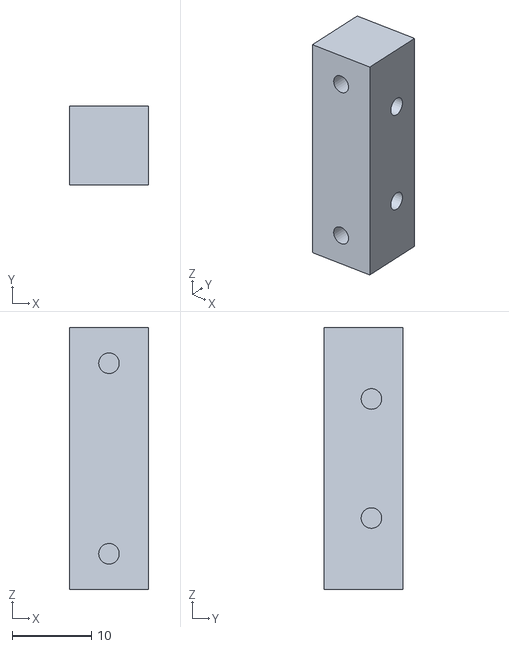
[picture p112: CAD file, 2018-05-28]
parts/avionics/bendix-king-kt-76c/side_bracket.stl
10.0 x 10.0 x 33.0
