allanglen/c172-flight-sim-panel/parts/avionics/garmin-gns-430/button_medium.stl

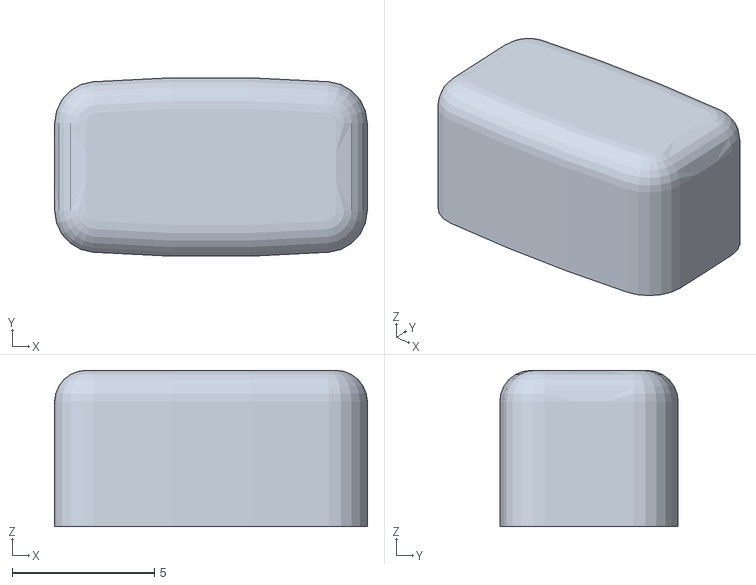
[picture p113: CAD file, 2018-01-07]
parts/avionics/garmin-gns-430/button_medium.stl
11.0 x 6.28 x 5.50
