allanglen/c172-flight-sim-panel/parts/avionics/garmin-gns-530/display_mounting_clips.stl

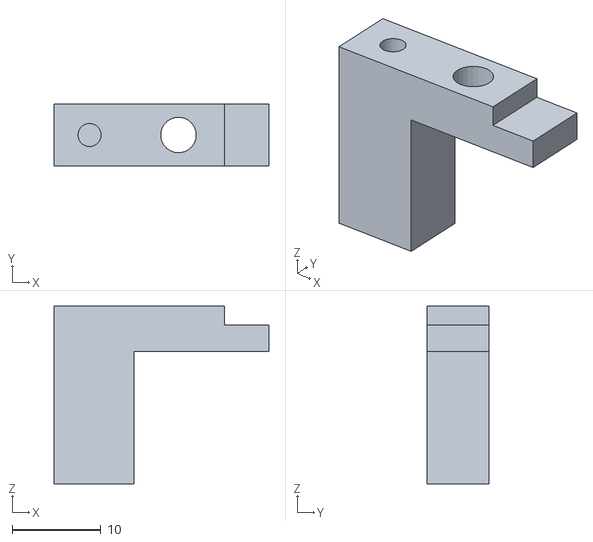
[picture p114: CAD file, 2018-01-21]
parts/avionics/garmin-gns-530/display_mounting_clips.stl
24.2 x 7.00 x 20.0
