allanglen/c172-flight-sim-panel/parts/flap-control-panel/flap_frame_mounting_bracket.stl

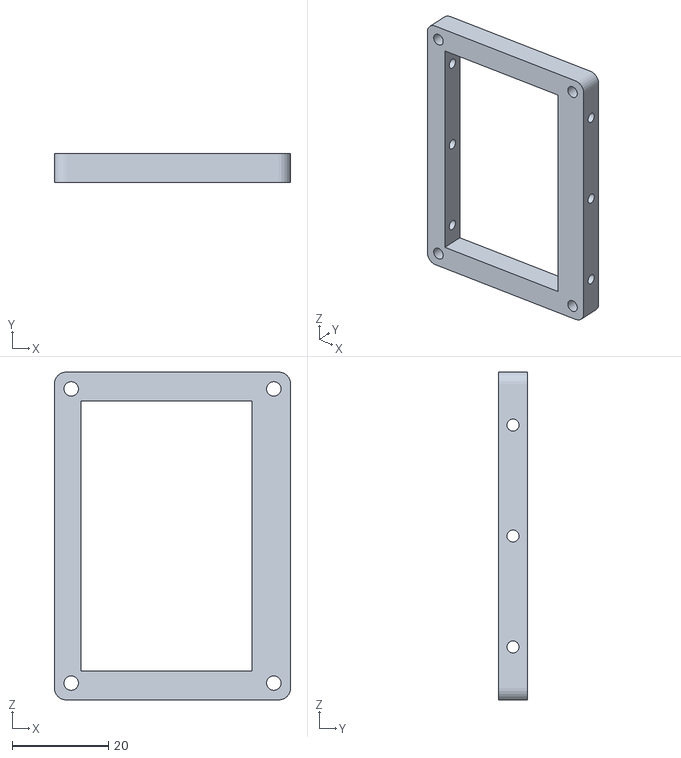
[picture p115: CAD file, 2017-12-20]
parts/flap-control-panel/flap_frame_mounting_bracket.stl
49.0 x 6.00 x 68.0
