allanglen/c172-flight-sim-panel/parts/instrument-panel/bezel_clock_button.FCStd

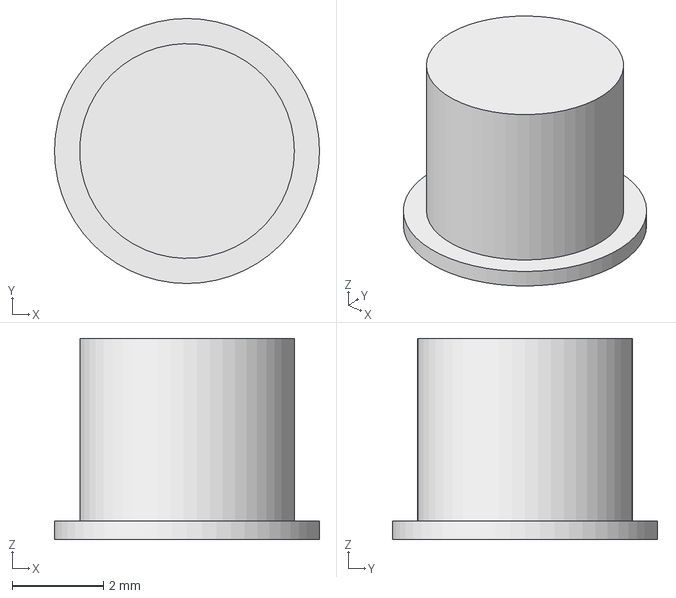
[picture p116: CAD file, 2017-12-05]
parts/instrument-panel/bezel_clock_button.FCStd
5.80 x 5.80 x 4.40 mm
