allanglen/c172-flight-sim-panel/parts/throttle-mixture-panel/mixture_knob.FCStd

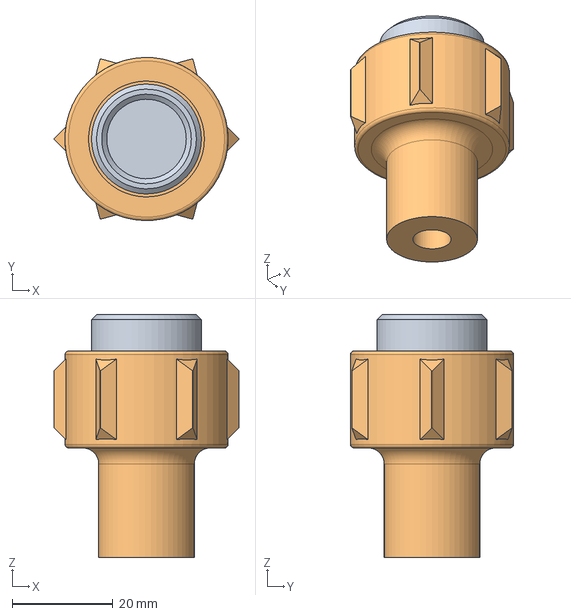
[picture p117: CAD file, 2017-12-18]
parts/throttle-mixture-panel/mixture_knob.FCStd
36.7 x 32.4 x 48.3 mm
Revolution (button)
Fusion (knob)
