allanglen/c172-flight-sim-panel/parts/avionics/bendix-king-kt-76c/bezel.stl

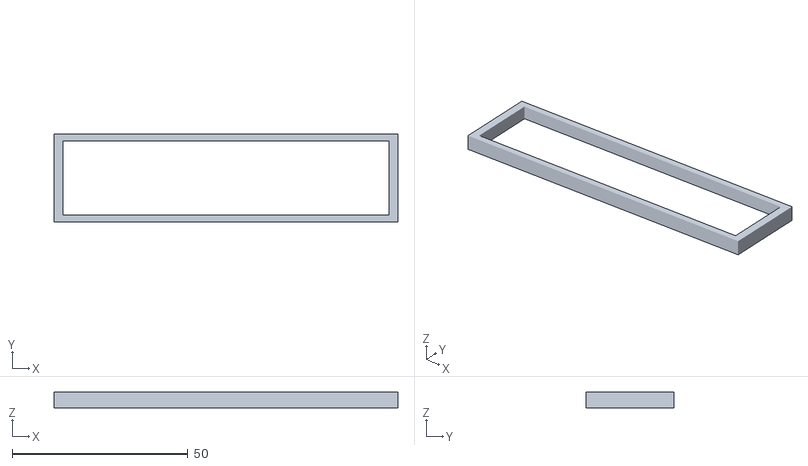
[picture p118: CAD file, 2018-05-28]
parts/avionics/bendix-king-kt-76c/bezel.stl
98.0 x 25.0 x 4.50
