allanglen/c172-flight-sim-panel/parts/avionics/garmin-gns-430/button_small.stl

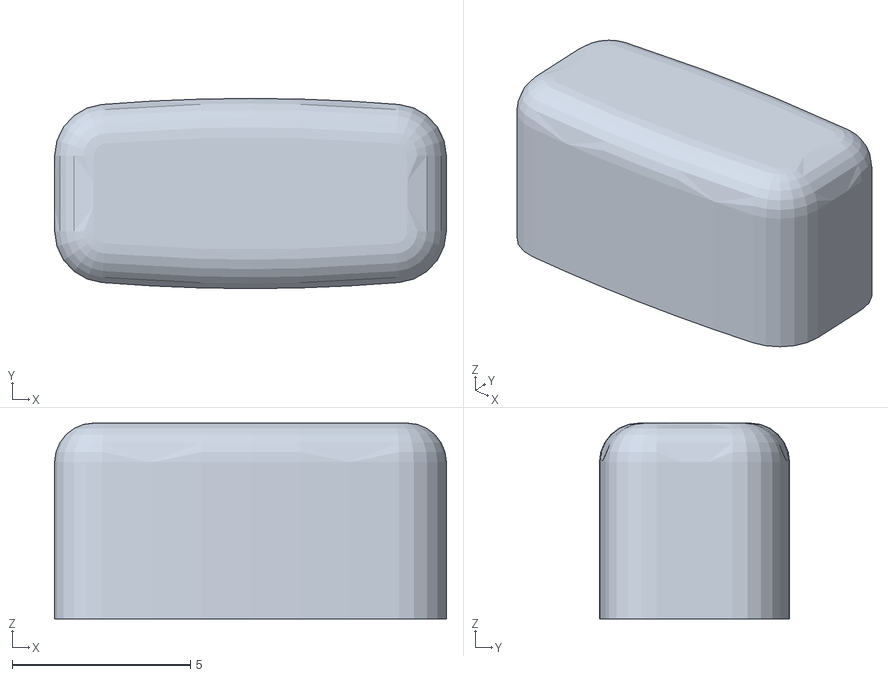
[picture p119: CAD file, 2018-01-07]
parts/avionics/garmin-gns-430/button_small.stl
11.0 x 5.34 x 5.50
