allanglen/c172-flight-sim-panel/parts/avionics/garmin-gns-530/display_electronics_mount_block.stl

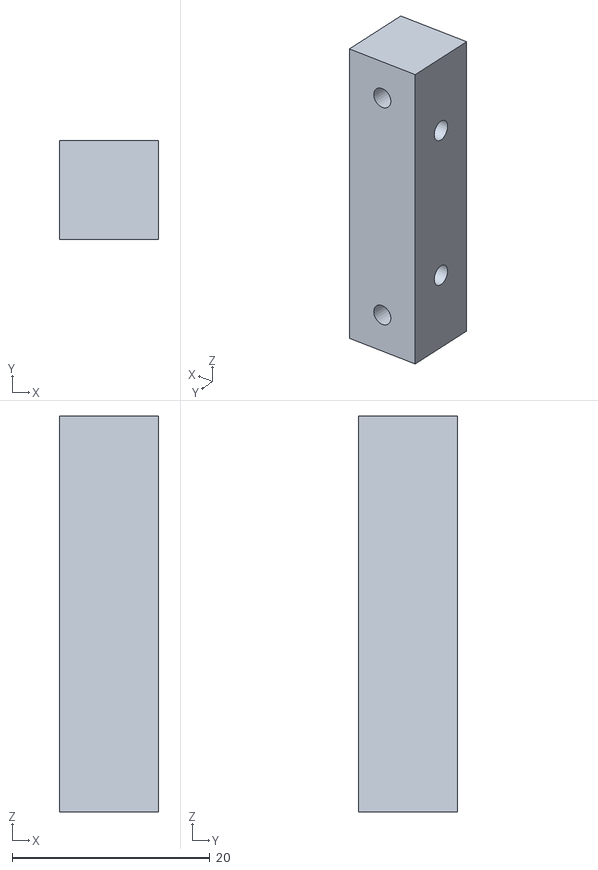
[picture p120: CAD file, 2018-01-21]
parts/avionics/garmin-gns-530/display_electronics_mount_block.stl
10.0 x 10.0 x 40.0
