allanglen/c172-flight-sim-panel/parts/instrument-panel/bezel_large_dual_encoder.stl

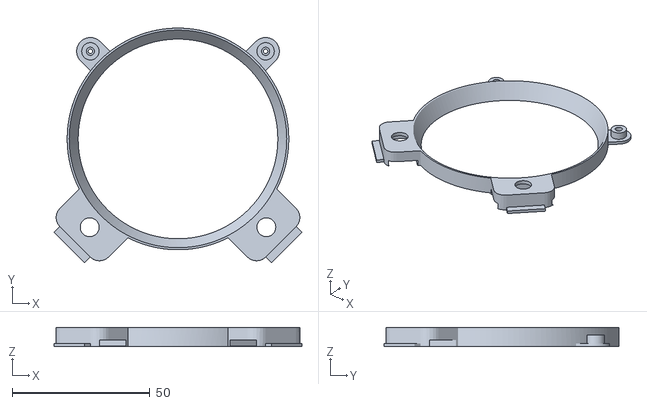
[picture p121: CAD file, 2017-12-05]
parts/instrument-panel/bezel_large_dual_encoder.stl
90.1 x 85.3 x 7.00
