allanglen/c172-flight-sim-panel/parts/avionics/garmin-gns-430/knob_outer.stl

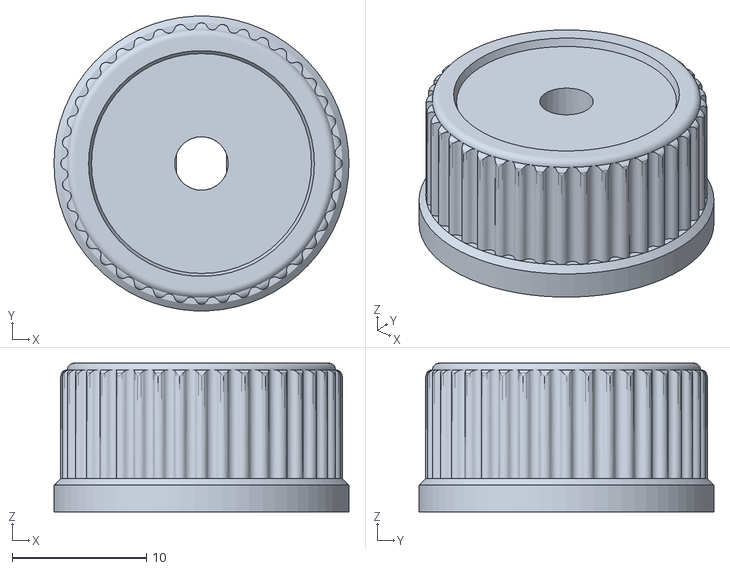
[picture p122: CAD file, 2017-12-30]
parts/avionics/garmin-gns-430/knob_outer.stl
22.0 x 22.0 x 11.1
