allanglen/c172-flight-sim-panel/parts/avionics/garmin-gns-530/display_bezel.stl

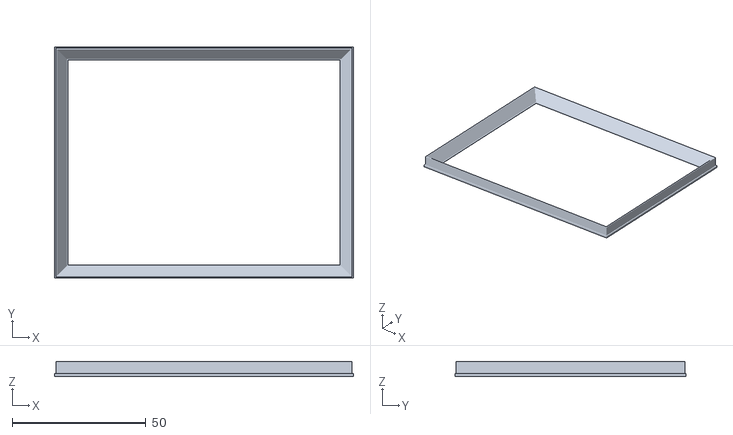
[picture p123: CAD file, 2018-01-21]
parts/avionics/garmin-gns-530/display_bezel.stl
111.7 x 86.4 x 5.50
