allanglen/c172-flight-sim-panel/parts/flap-control-panel/flap_position_indicator.stl

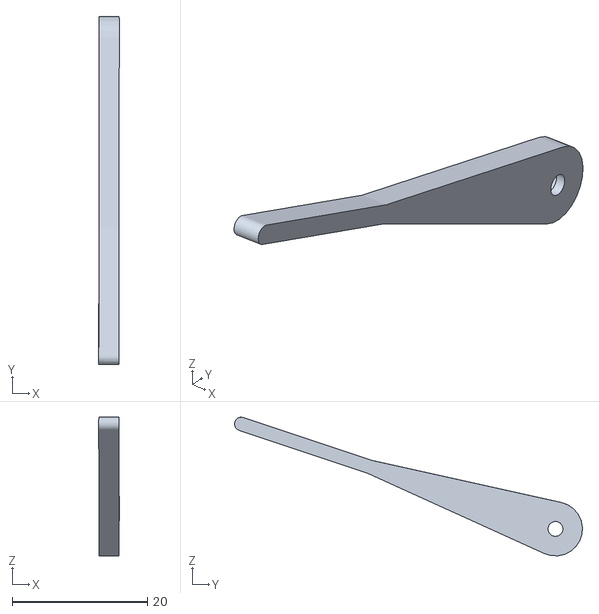
[picture p124: CAD file, 2017-12-20]
parts/flap-control-panel/flap_position_indicator.stl
3.04 x 51.5 x 20.5
