allanglen/c172-flight-sim-panel/parts/instrument-panel/bezel_small_egt.stl

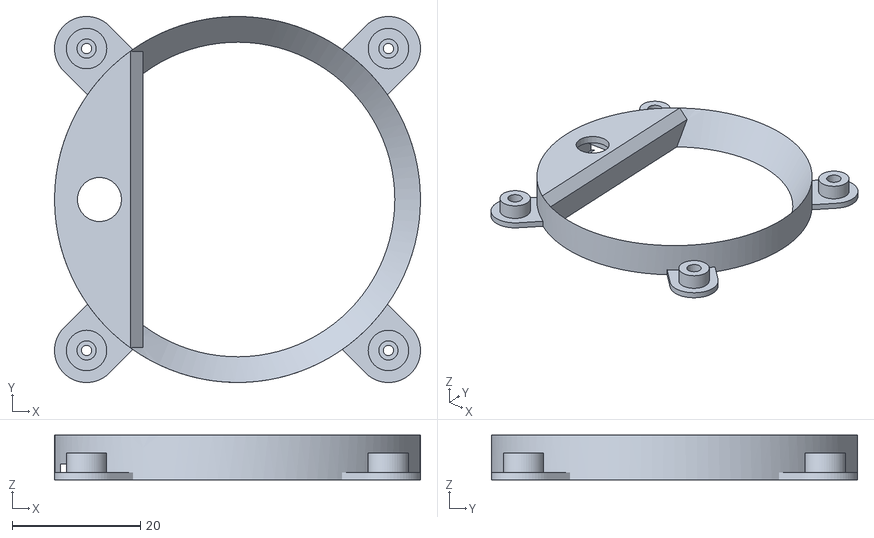
[picture p125: CAD file, 2017-12-05]
parts/instrument-panel/bezel_small_egt.stl
57.0 x 57.0 x 7.00
