allanglen/c172-flight-sim-panel/parts/throttle-mixture-panel/throttle_knob.FCStd

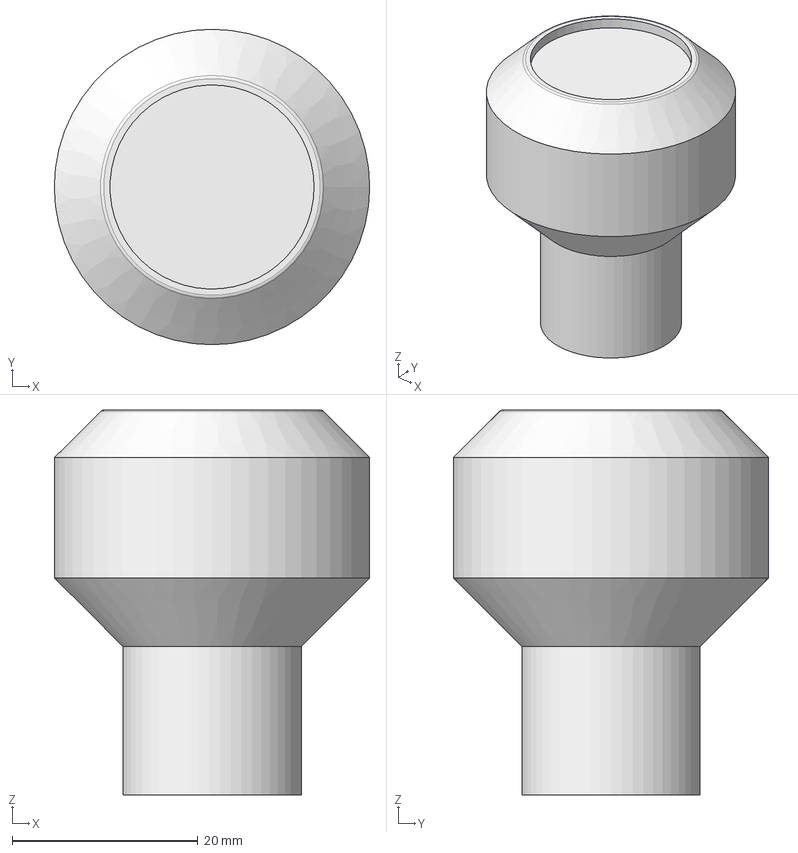
[picture p126: CAD file, 2017-12-18]
parts/throttle-mixture-panel/throttle_knob.FCStd
34.0 x 34.0 x 41.5 mm
