allanglen/c172-flight-sim-panel/parts/avionics/garmin-gns-430/display_bezel.stl

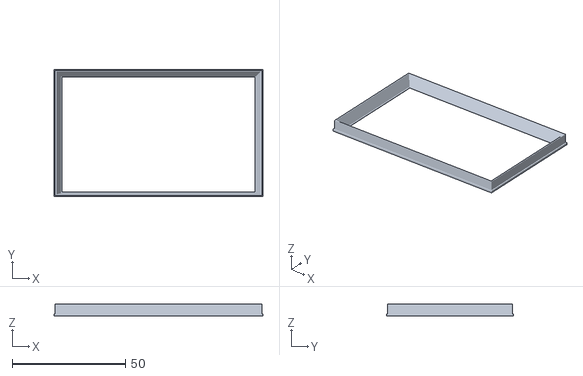
[picture p127: CAD file, 2017-12-30]
parts/avionics/garmin-gns-430/display_bezel.stl
92.2 x 56.2 x 5.50
