allanglen/c172-flight-sim-panel/parts/flap-control-panel/flap_faceplate.stl

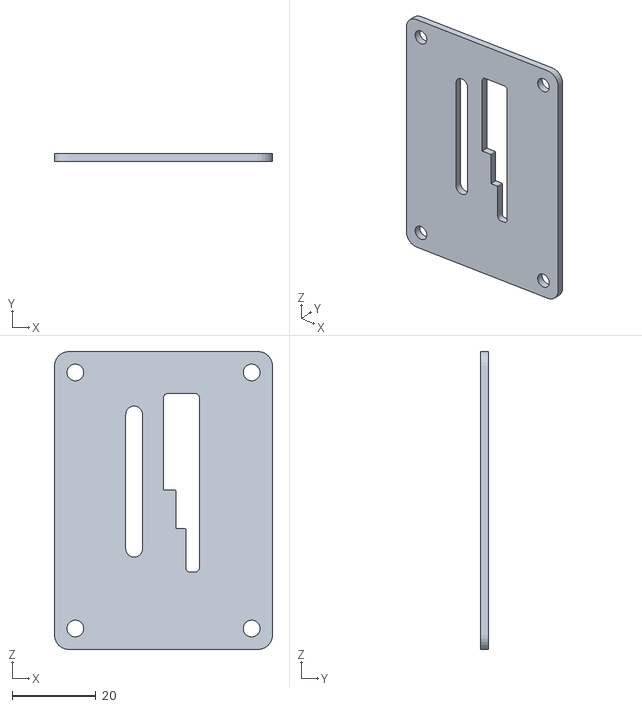
[picture p128: CAD file, 2017-12-20]
parts/flap-control-panel/flap_faceplate.stl
52.0 x 2.00 x 71.0
