allanglen/c172-flight-sim-panel/parts/instrument-panel/bezel_large_attitude.stl

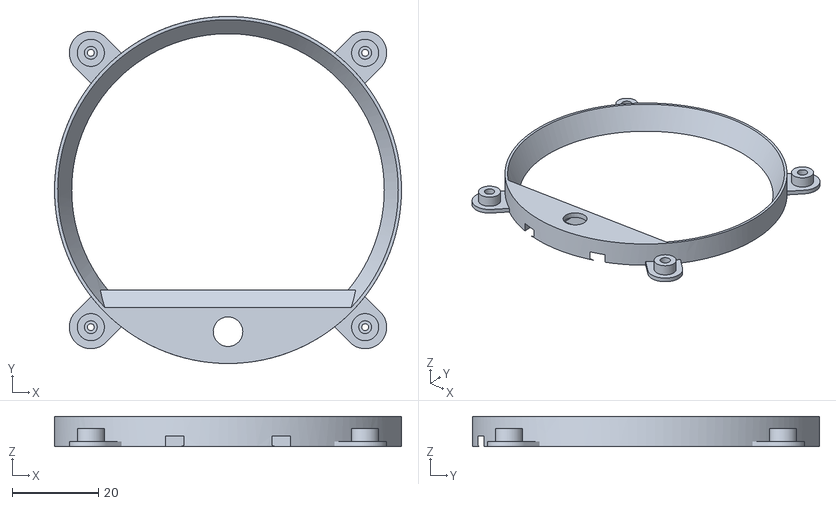
[picture p129: CAD file, 2017-12-05]
parts/instrument-panel/bezel_large_attitude.stl
80.5 x 80.5 x 7.00
