allanglen/c172-flight-sim-panel/parts/throttle-mixture-panel/mixture_button.stl

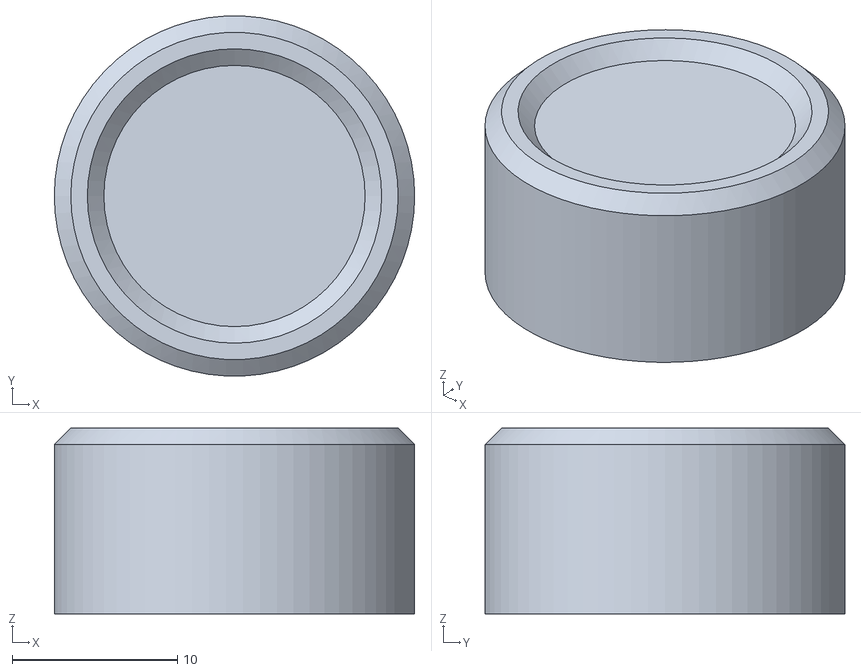
[picture p130: CAD file, 2017-12-18]
parts/throttle-mixture-panel/mixture_button.stl
21.8 x 21.8 x 11.2
