allanglen/c172-flight-sim-panel/parts/avionics/garmin-gns-430/display_clip.FCStd

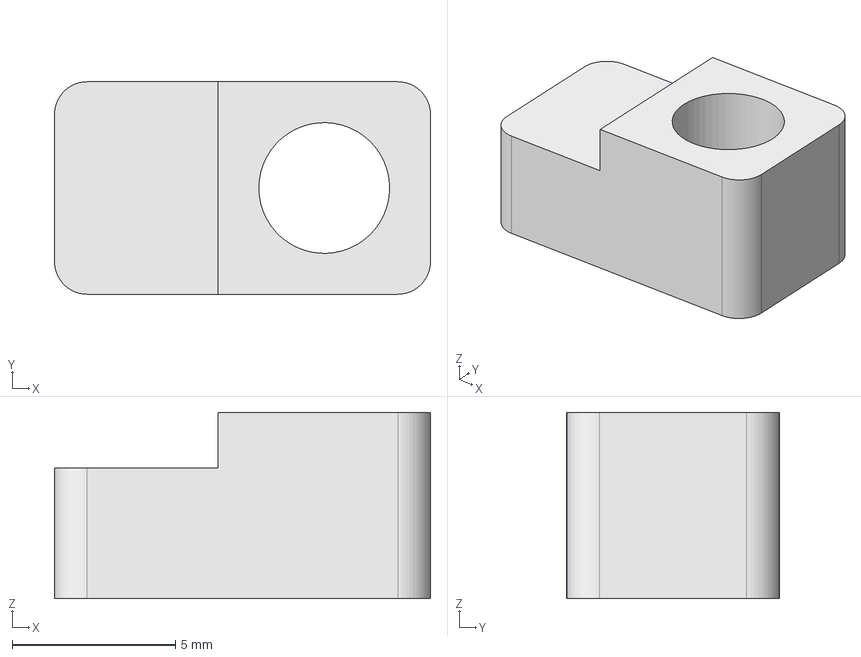
[picture p131: CAD file, 2017-12-30]
parts/avionics/garmin-gns-430/display_clip.FCStd
11.5 x 6.50 x 5.70 mm
