allanglen/c172-flight-sim-panel/parts/flap-control-panel/flap_frame_left.stl

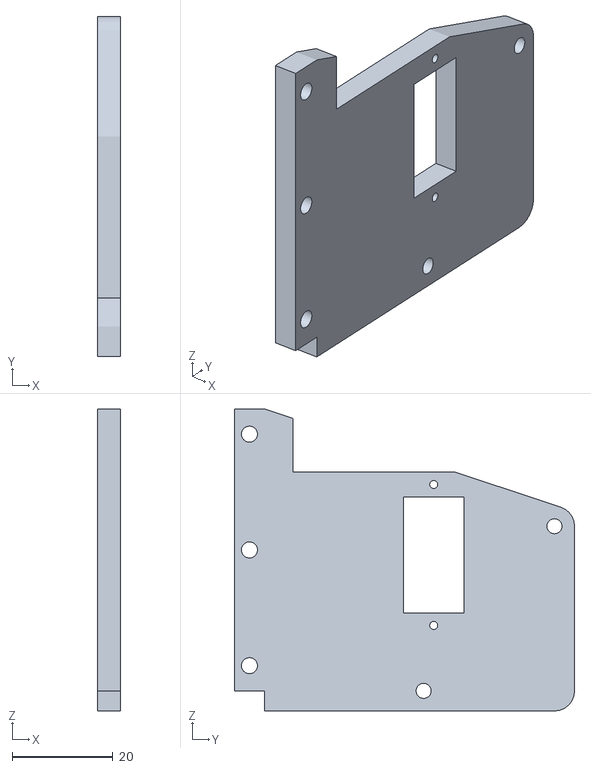
[picture p132: CAD file, 2017-12-20]
parts/flap-control-panel/flap_frame_left.stl
4.50 x 67.6 x 60.0
