allanglen/c172-flight-sim-panel/parts/instrument-panel/bezel_large_single_encoder.stl

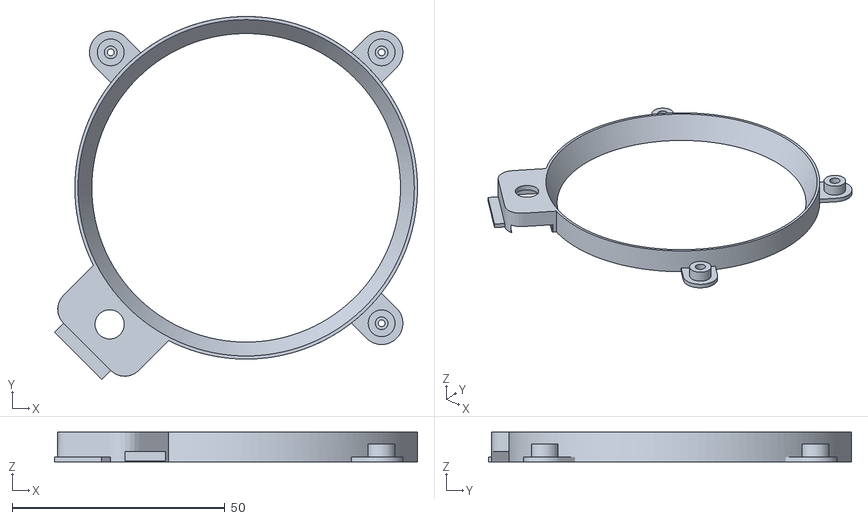
[picture p133: CAD file, 2017-12-05]
parts/instrument-panel/bezel_large_single_encoder.stl
85.3 x 85.3 x 7.00
