allanglen/c172-flight-sim-panel/parts/throttle-mixture-panel/rheostat_knob_inner.stl

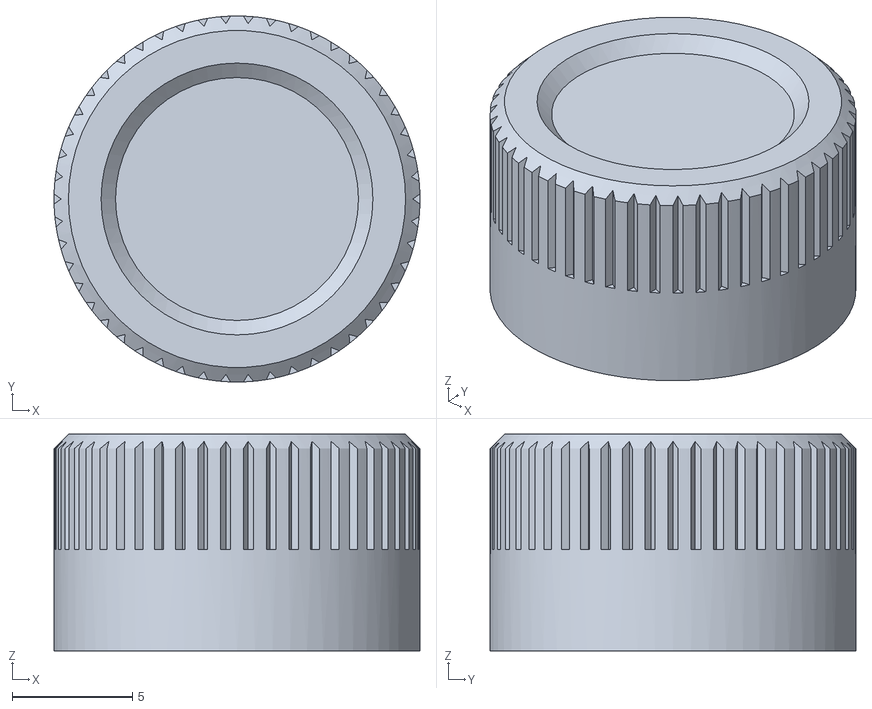
[picture p134: CAD file, 2017-12-18]
parts/throttle-mixture-panel/rheostat_knob_inner.stl
15.2 x 15.2 x 9.00
