allanglen/c172-flight-sim-panel/parts/avionics/garmin-gns-430/frame_mount_bracket.stl

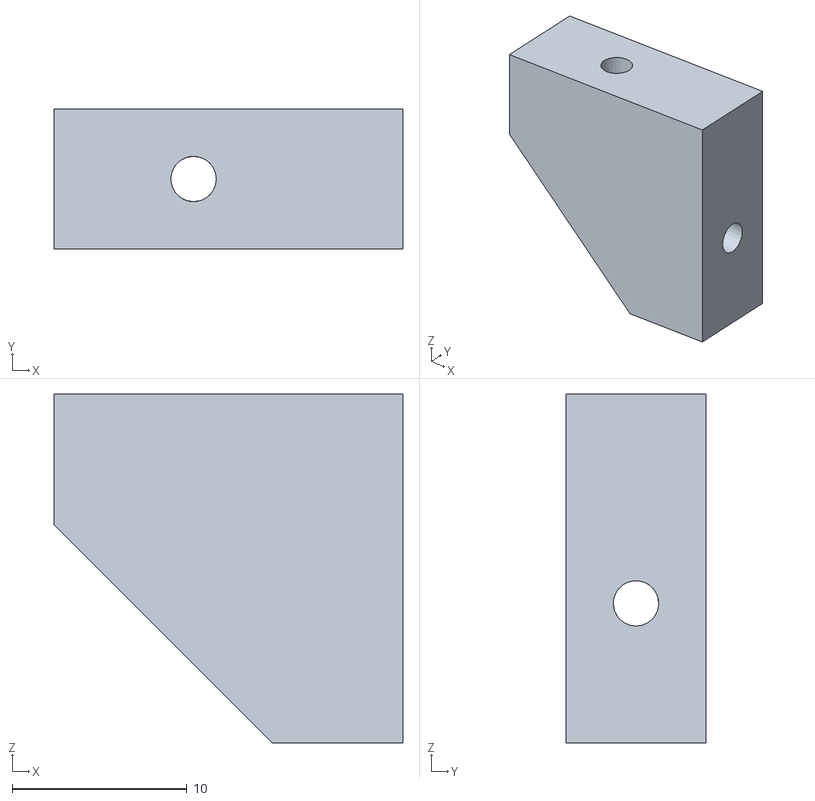
[picture p135: CAD file, 2017-12-30]
parts/avionics/garmin-gns-430/frame_mount_bracket.stl
20.0 x 8.00 x 20.0
