allanglen/c172-flight-sim-panel/parts/flap-control-panel/flap_handle.FCStd

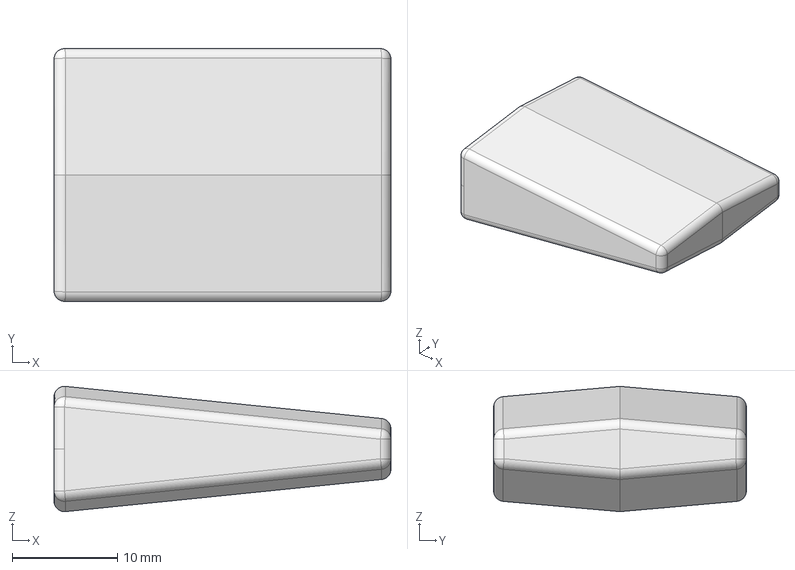
[picture p136: CAD file, 2017-12-20]
parts/flap-control-panel/flap_handle.FCStd
32.0 x 24.0 x 11.9 mm
