allanglen/c172-flight-sim-panel/parts/instrument-panel/bezel_large_router_guide.FCStd

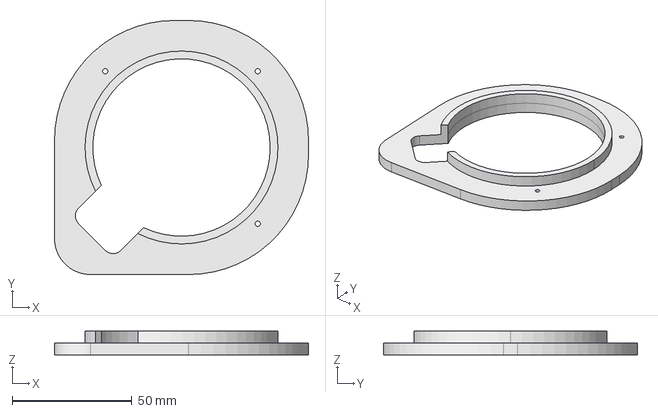
[picture p137: CAD file, 2017-12-05]
parts/instrument-panel/bezel_large_router_guide.FCStd
106.0 x 106.0 x 10.0 mm
