allanglen/c172-flight-sim-panel/parts/throttle-mixture-panel/rheostat_knob_outer.stl

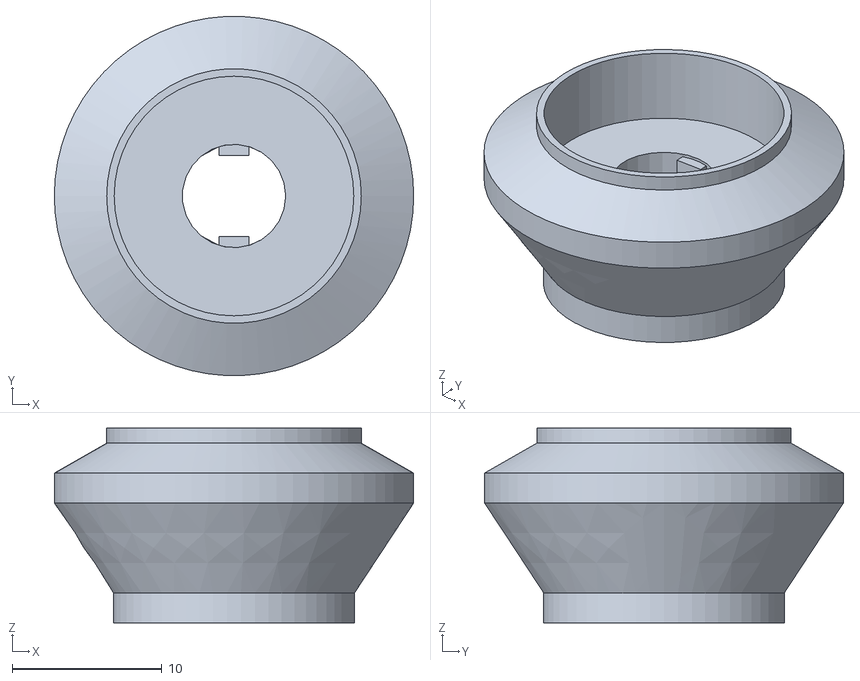
[picture p138: CAD file, 2017-12-18]
parts/throttle-mixture-panel/rheostat_knob_outer.stl
24.0 x 24.0 x 13.0
