allanglen/c172-flight-sim-panel/parts/avionics/garmin-gns-430/knob_inner.stl

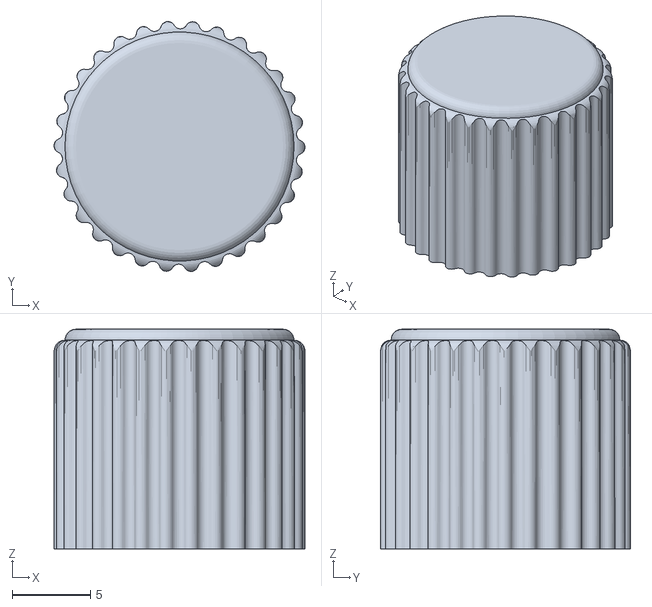
[picture p139: CAD file, 2017-12-30]
parts/avionics/garmin-gns-430/knob_inner.stl
16.0 x 15.9 x 14.0
