allanglen/c172-flight-sim-panel/parts/instrument-panel/bezel_annunciator.FCStd

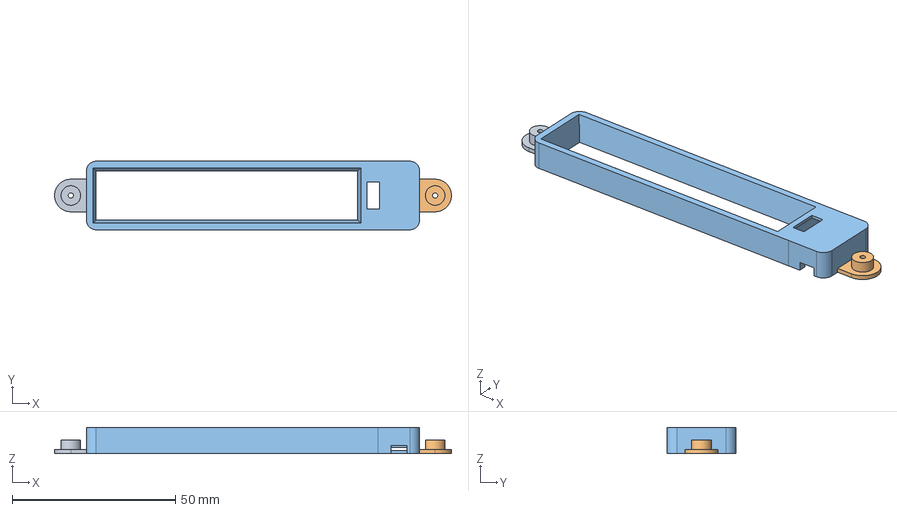
[picture p140: CAD file, 2017-12-05]
parts/instrument-panel/bezel_annunciator.FCStd
121.5 x 21.0 x 8.00 mm
Clone of Pocket
