allanglen/c172-flight-sim-panel/parts/avionics/garmin-gns-430/button_zoom.stl

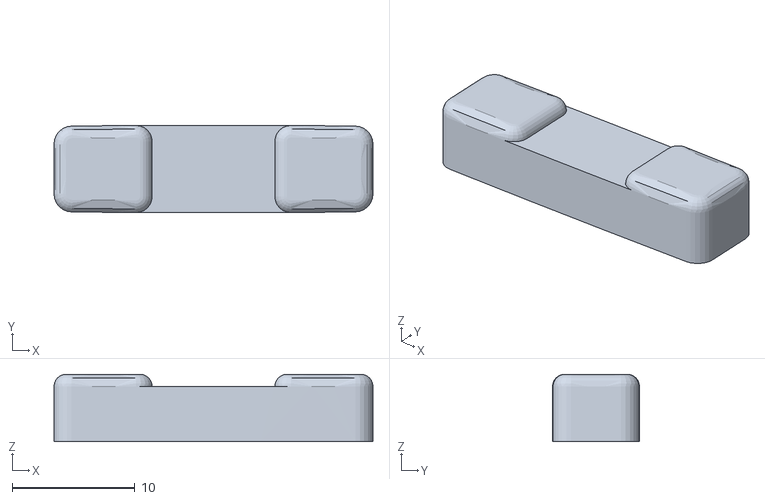
[picture p141: CAD file, 2017-12-30]
parts/avionics/garmin-gns-430/button_zoom.stl
26.0 x 7.13 x 5.50
