allanglen/c172-flight-sim-panel/parts/avionics/garmin-gns-530/knob_volume.FCStd

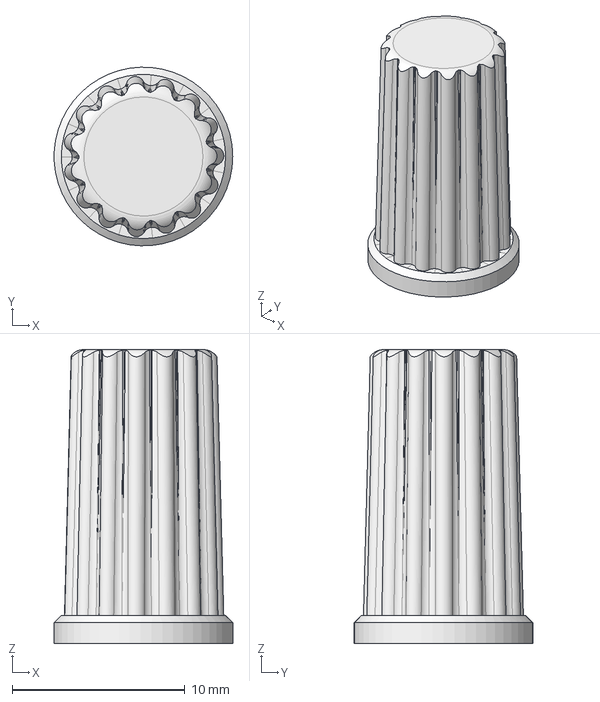
[picture p142: CAD file, 2017-12-30]
parts/avionics/garmin-gns-530/knob_volume.FCStd
10.3 x 10.3 x 17.0 mm
