allanglen/c172-flight-sim-panel/parts/avionics/garmin-gns-430/knob.FCStd

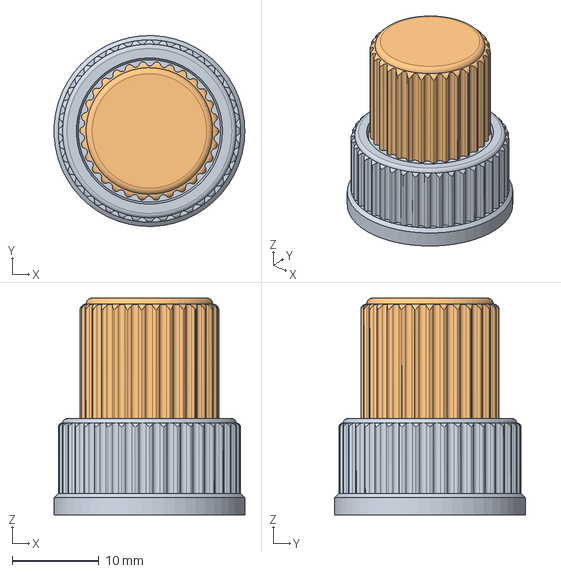
[picture p143: CAD file, 2017-12-30]
parts/avionics/garmin-gns-430/knob.FCStd
22.0 x 22.0 x 25.0 mm
Cut (outer)
Cut (inner)
