allanglen/c172-flight-sim-panel/docs/assets/images/ardsimx/arduino_wiring.jpg

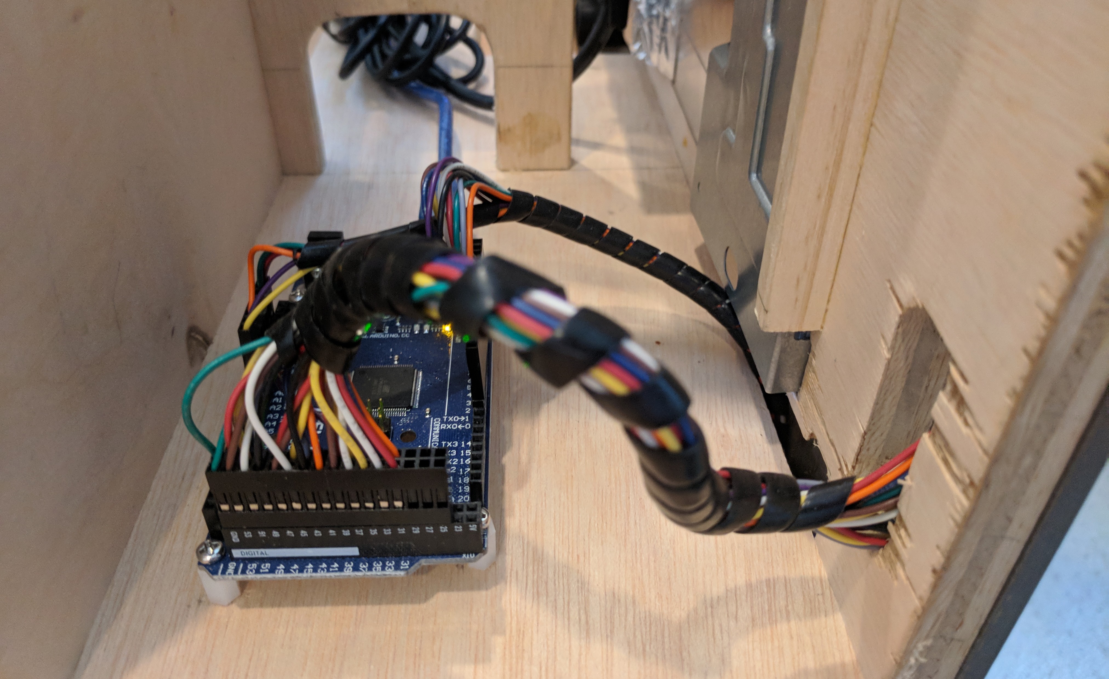
docs/assets/images/ardsimx/arduino_wiring.jpg
