allanglen/c172-flight-sim-panel/docs/assets/images/garmin-gns-530/assembly_rear.jpg

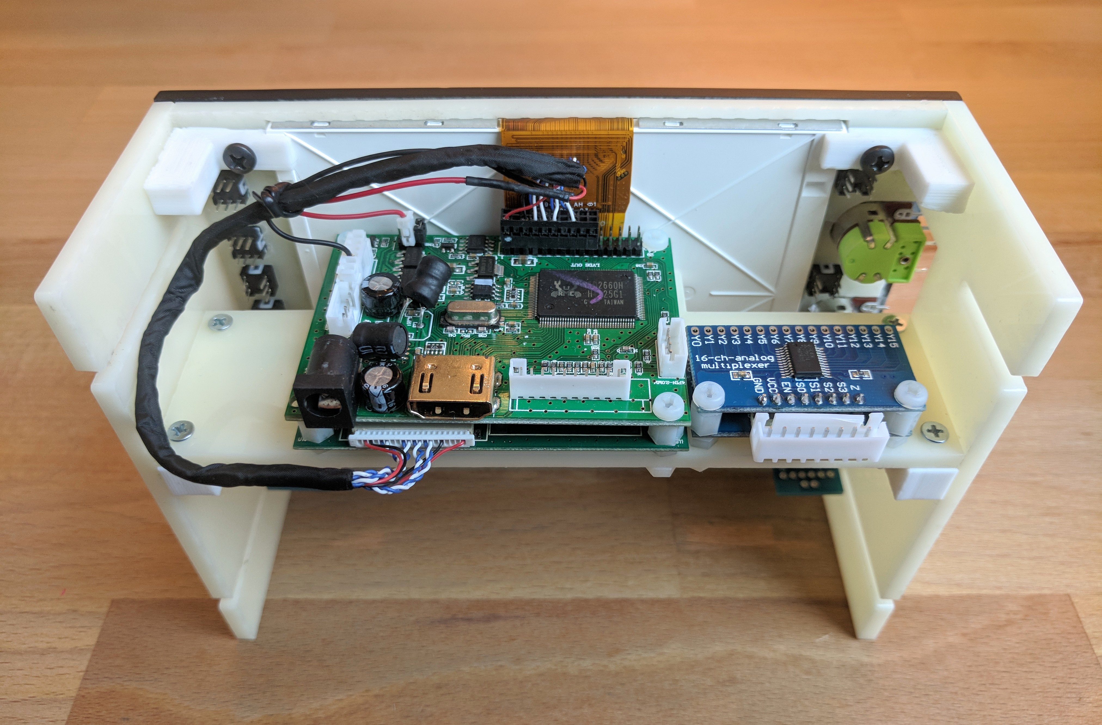
docs/assets/images/garmin-gns-530/assembly_rear.jpg
