allanglen/c172-flight-sim-panel/docs/assets/images/instrument-panel/bezels_installed.jpg

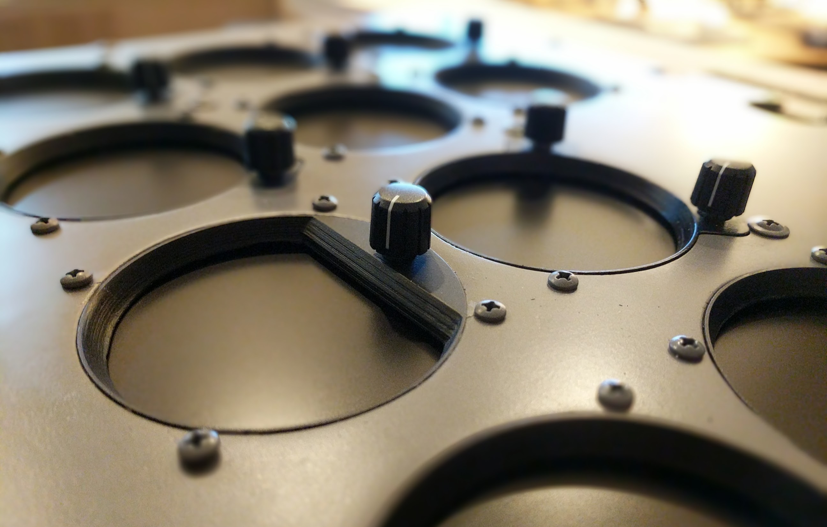
docs/assets/images/instrument-panel/bezels_installed.jpg
