allanglen/c172-flight-sim-panel/docs/assets/images/instrument-panel/wiring_routing_01.jpg

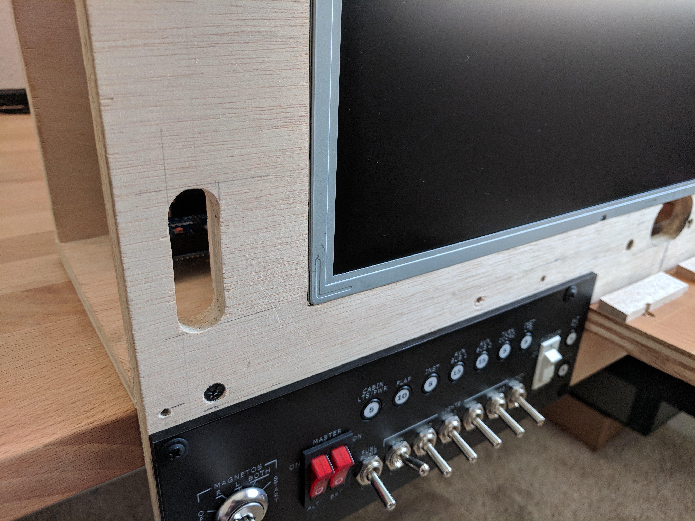
docs/assets/images/instrument-panel/wiring_routing_01.jpg
